RicardoCSR/MinervaProject/Render Nixie 1.png

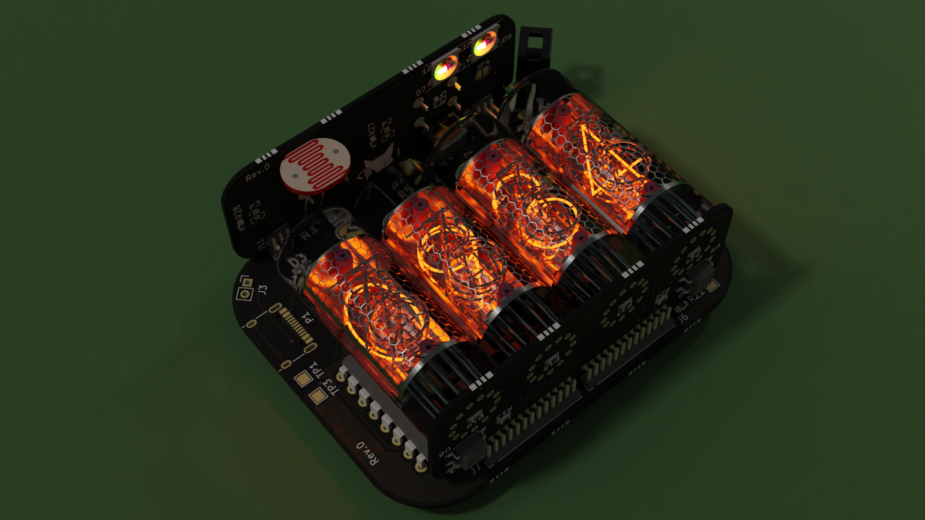
Render Nixie 1.png
