RicardoCSR/MinervaProject/Render 1.png

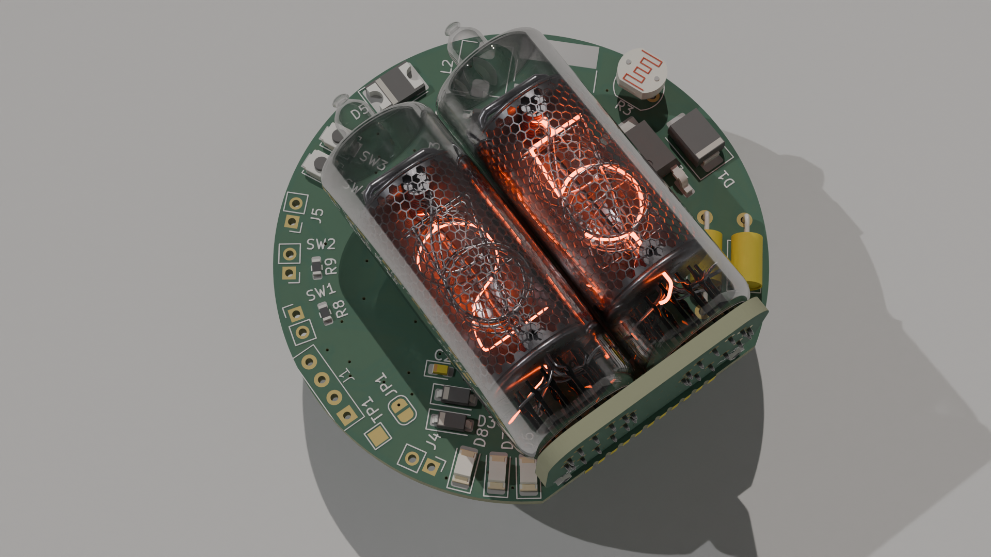
Render 1.png
