RicardoCSR/MinervaProject/Arquivos Web Minerva Clock/2.jpg

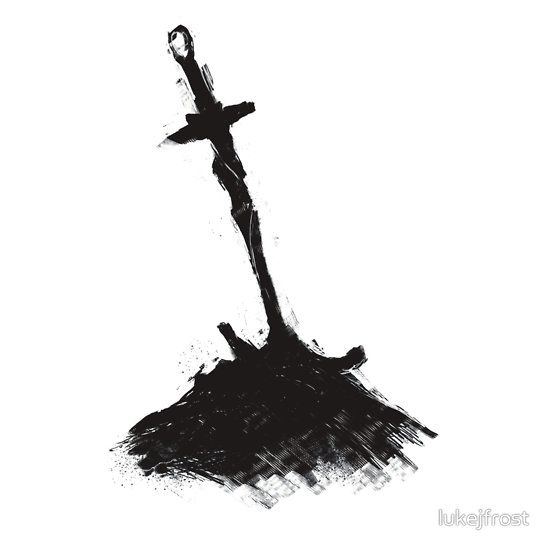
Arquivos Web Minerva Clock/2.jpg
