RicardoCSR/MinervaProject/Arquivos Web Minerva Clock/3.jpg

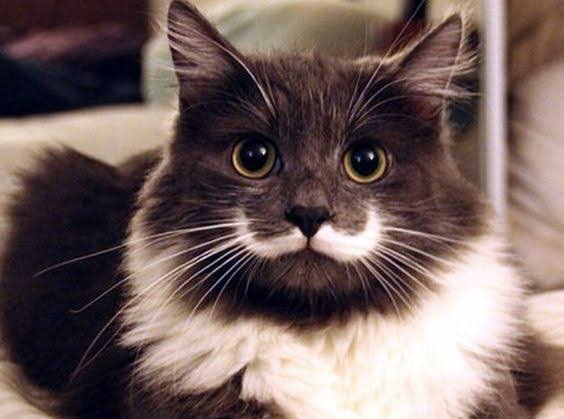
Arquivos Web Minerva Clock/3.jpg
