RicardoCSR/MinervaProject/Arquivos Web Minerva Clock/5.jpg

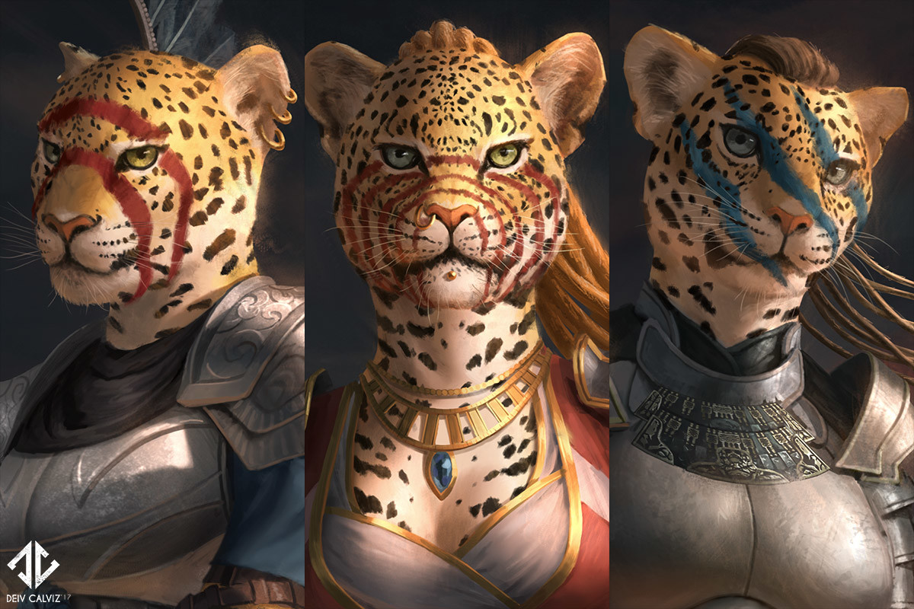
Arquivos Web Minerva Clock/5.jpg
