RicardoCSR/MinervaProject/Arquivos Web Minerva Clock/backgroundres.png

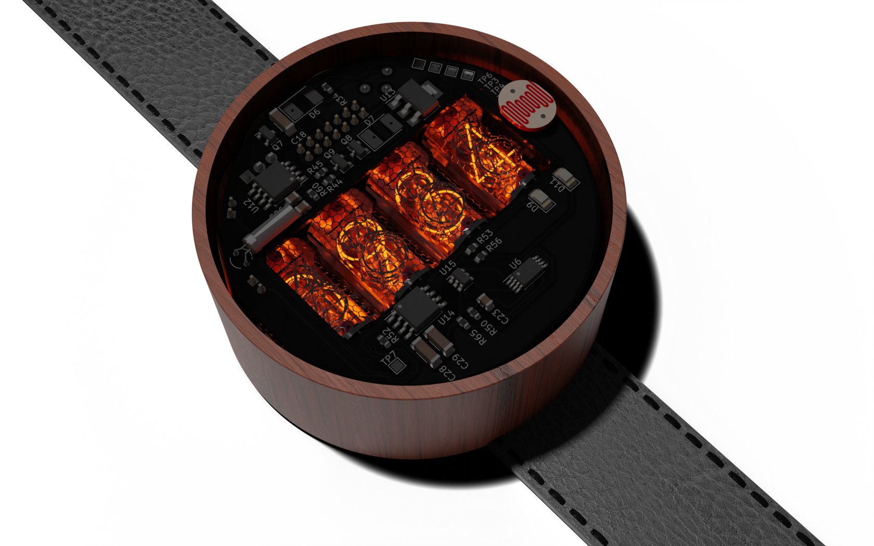
Arquivos Web Minerva Clock/backgroundres.png
