RicardoCSR/MinervaProject/ESP32 Conf 232.webp

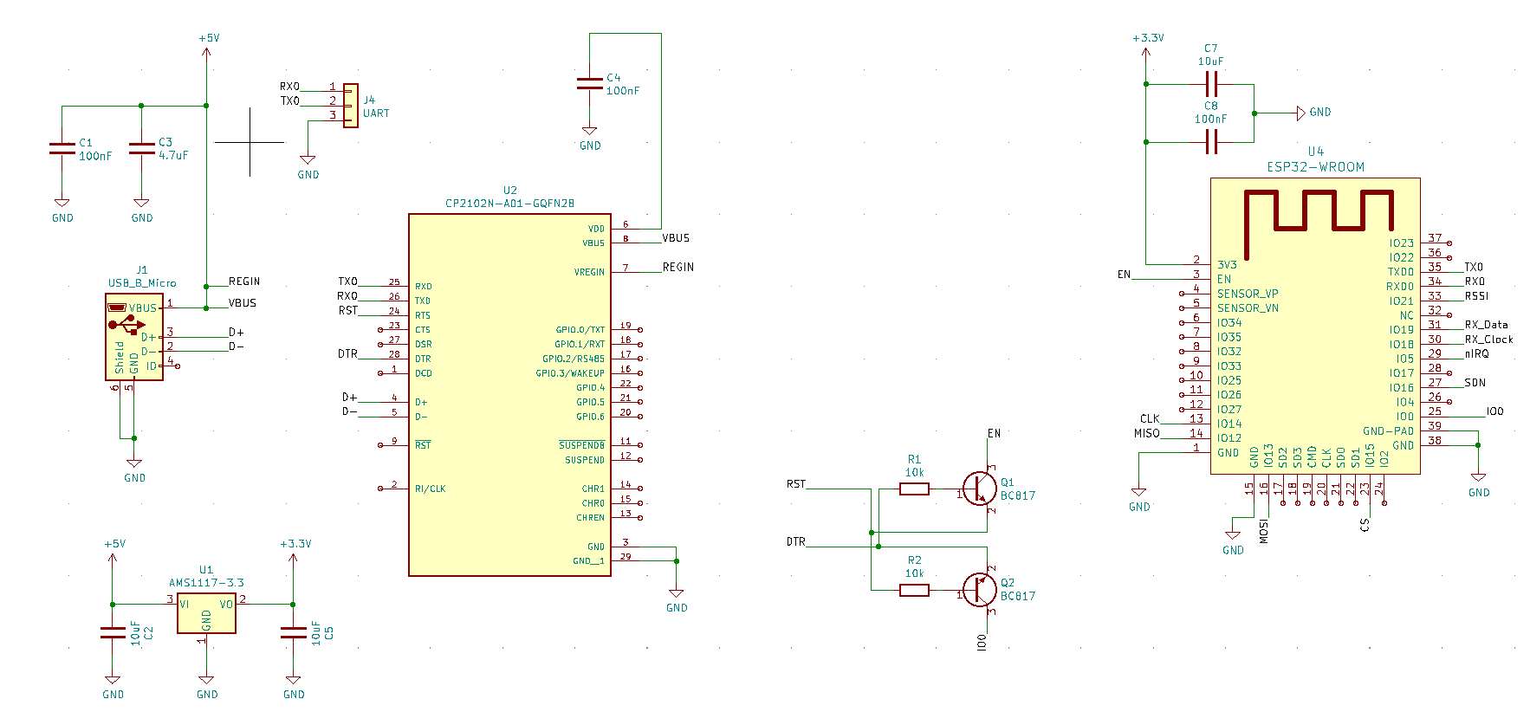
ESP32 Conf 232.webp
