RicardoCSR/MinervaProject/Imagens/Plano Fundo/Nixie.png

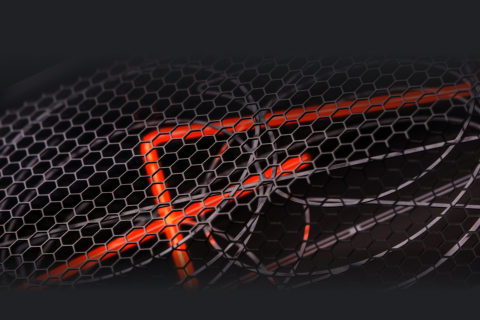
Imagens/Plano Fundo/Nixie.png
