RicardoCSR/MinervaProject/Web Server/Frame 61.jpg

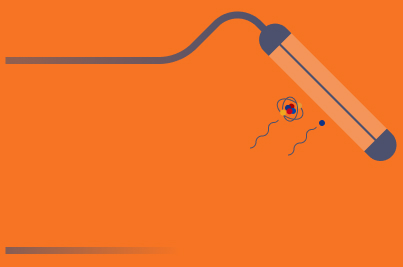
Web Server/Frame 61.jpg
