RicardoCSR/MinervaProject/Web Server/Frame 62.jpg

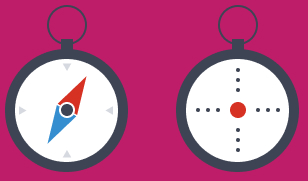
Web Server/Frame 62.jpg
