RicardoCSR/MinervaProject/Web Server/Frame 63.jpg

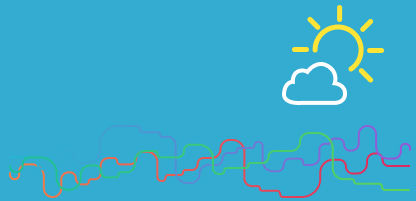
Web Server/Frame 63.jpg
