RicardoCSR/MinervaProject/Web Server/Frame 64.jpg

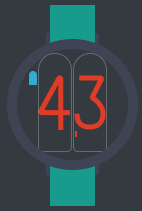
Web Server/Frame 64.jpg
