RicardoCSR/MinervaProject/Web Server/WebServer/blackmufox.jpg

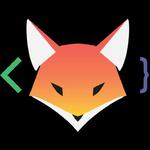
Web Server/WebServer/blackmufox.jpg
