RicardoCSR/MinervaProject/Web Server/WebServer/blackmufoxpng.png

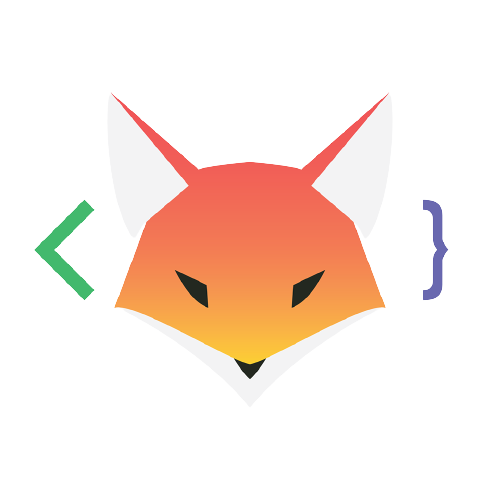
Web Server/WebServer/blackmufoxpng.png
