RicardoCSR/MinervaProject/Web Server/WebServer/simplemufox.jpg

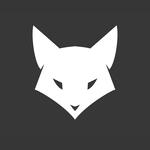
Web Server/WebServer/simplemufox.jpg
