RicardoCSR/MinervaProject/Relogio_STM32_TFT_Nixie.ino

 /*
Lista Terminais Utilizados STM32F401CCU6

BRANCO -    COMANDOS (BOTOES)
VERDE -     GNDS   
AMARELO -   3V3
VERMELHO -  5V
PRETO -     PWM
LARANJA -   SPI
ROXO -      GEIGER     
AZUL -      NIXIE

Caracteristica

SN74141 : True Table
calcDay1 C B A #
L,L,L,L 0
L,L,L,H 1
L,L,H,L 2
L,L,H,H 3
L,H,L,L 4
L,H,L,H 5
L,H,H,L 6
L,H,H,H 7
H,L,L,L 8
H,L,L,H 9
H,L,H,L N
H,L,H,H N
H,H,L,L N
H,H,L,H N
H,H,H,L N
H,H,H,H N

*/

// DADOS RELOGIO
int fulltime;                   // Armazena Horario 4 Digitos Processado
int hours = 0;                  // Armazena Horario Horas
int mins = 0;                   // Armazena Horario Minutos
byte compareTimeHour;           // Armazena Horario do Display
byte compareTimeMins;           // Armazena Horario do Display
byte compareTimeSecs;           // Armazena Horario do Display

byte compareSecs = 0;           // Armazena Horario Menu de Ajuste Relogio
byte compareMins = 0;           // Armazena Horario Menu de Ajuste Relogio
byte compareHour = 0;           // Armazena Horario Menu de Ajuste Relogio

byte compareDay = 0;            // Armazena Data Menu de Ajuste Calendario
byte compareMonth = 0;          // Armazena Data Menu de Ajuste Calendario
int compareYear = 0;            // Armazena Data Menu de Ajuste Calendario

byte hourBias;                  // Byte para Long horas x fuso (12 ~ 24)
byte minuteBias;                // Byte para Long minutos x 60 
byte secsBias;                  // Byte para Long segundos x 60
int secs;                       // Armazena Horario Segundos sem conversão

// NIVEL DE BATERIA E WIFI   
byte compareUpdateBattery;      // Armazena atualização de updateBattery
byte compareUpdateWiFi;         // Armazena atualização de updateBattery


// DADOS TOUCHSCREEN
int xMax;
int xMin;
int yMax;
int yMin;

// DADOS TIMERS
unsigned long period = 0;

// VALORES AJUSTAVEIS PELO USUÁRIO
byte logoTime = 3;

byte backgroundSetup = 0;
// backgroundSetup = 0 Programa Fundo Preto e Colorido.
// backgroundSetup = 1 Programa Fundo Branco e Colorido.
// backgroundSetup = 2 Programa Fundo Preto.
// backgroundSetup = 3 Programa Fundo Branco.

byte batteryStyleMode = 0;
// batteryStyleMode = 0 Estilo 1 de Bateria.
// batteryStyleMode = 1 Estilo 2 de Bateria.
// batteryStyleMode = 2 Estilo 3 de Bateria.
// batteryStyleMode = 3 Estilo 4 de Bateria.

byte lockStyle = 0;
// lockStyle = 0 Estilo 1 de Trava.
// lockStyle = 1 Estilo 2 de Trava.

int day;                        // Armazena dados de dia calendario
int month;                      // Armazena dados de mes calendario
int year;                       // Armazena dados de ano calendario
int startDay = 0;               // Identifica o 1 dia da semana
byte Week = 0;                  // Armazena Semana do ano
int dayWeek = 0;                // Armazena Dia do ano
int monthLengh = 0;             // Armazena o tamanho do Mes
int newDayStart = 0;            // Armazena o Dia do inicio da semana
int newWeekStart = 0;           // Armazena a posicao da Semana 
byte weekYear = 1;              // Armazena semana do mes calendario
int udpateCalendar;             // Armazena o dia para atualizacao do calendario

byte fuso = 1;                  
//fuso = 0 12 Horas  
//fuso = 1 24 Horas

// GERACAO DE GRAFICOS
int secsCalcGeiger = 0;         // Armazena segundos marcação gráfico Geiger
int minsCalcGeiger = 0;         // Armazena minutos marcação gráfico Geiger
int minsCalcTemp = 0;           // Armazena Horario marcação gráfico Temperatura
int minsCalcHumi = 0;           // Armazena Horario marcação gráfico Umidade
int minsCalcPres = 0;           // Armazena Horario marcação gráfico Pressão Atmosferica

int calcGeiger = 0;             // Armazena dado de Contagem para geigerCalc
int calcTemp = 0;               // Armazena dado de Contagem para tempCalc
int calcHumi = 0;               // Armazena dado de Contagem para humiCalc
int calcPres = 0;               // Armazena dado de Contagem para presCalc

int bankGeiger = 0;             // Armazena dado da posição do Gráfico em uso
int bankTemp = 0;               // Armazena dado da posição do Gráfico em uso
int bankHumi = 0;               // Armazena dado da posição do Gráfico em uso
int bankPres = 0;               // Armazena dado da posição do Gráfico em uso

byte functGeiger = 0;


int writerGeiger = 0;           // Armazena dado da posição do Gráfico em não uso
int writerTemp = 0;             // Armazena dado da posição do Gráfico em não uso
int writerHumi = 0;             // Armazena dado da posição do Gráfico em não uso
int writerPres = 0;             // Armazena dado da posição do Gráfico em não uso

int arrayGeiger [400] = {0};     // Armazena dados de Geiger
int arrayTemp [400] = {0};       // Armazena dados de Temperatura 
int arrayHumi [400] = {0};       // Armazena dados de Umidade 
int arrayPres [400] = {0};       // Armazena dados de Pressão Atmosferica

byte encoderPos = 0;
byte lastPos;
byte readClock;
boolean bCW;

int pressingDuration = 500;     // Tempo do botão Pressionado em Millis

unsigned long timerMode = 0;    // Armazena tempo atual
unsigned long touchMode = 0;    // Armazena tempo Touch

int minimumBrightness = 25;
int maximumBrightness = 255;

byte displayMode = 0;
// displayMode = 0 Sistema aguardando comando
// displayMode = 1 Habilita entrada do Menu
// displayMode = 2 Habilita saida do Menu

byte displayTFT = 0;     
// displayTFT = 0 Sistema aguardando comando

// BANCO DE DADOS DE COMPARADORES
byte logoStarted = 0;
// logoStarted = 0 Tela de Abertura ativado.
// logoStarted = 1 Tela de Abertura desativado.

byte powerCharger = 0;          
// powerCharger = 0 Carregador Desconectado
// powerCharger = 1 Carregador Conectado

byte screenLoad = 0;
// screenLoad = 0 Tela inicia o carregamento.
// screenLoad = 1 Tela para o carregamento.

byte updateBattery = 0;
// updateBattery = 0 Apresentação Bateria Level 1
// updateBattery = 1 Apresentação Bateria Level 2
// updateBattery = 2 Apresentação Bateria Level 3
// updateBattery = 3 Apresentação Bateria Level 4
// updateBattery = 4 Apresentação Bateria Level 5
// updateBattery = 5 Apresentação Bateria Level 6
// updateBattery = 6 Apresentação Bateria Level 7

byte wifiStyle = 0;
// wifiStyle = 0 Design WiFi default
// wifiStyle = 1 Design WiFi 1
// wifiStyle = 2 Design WiFi 2
// wifiStyle = 3 Design WiFi 3

byte wifiRead = 0;
// wifiRead = 0 WiFi em alta potência
// wifiRead = 1 WiFi em media potência
// wifiRead = 2 WiFi em baixa potência
// wifiRead = 3 WiFi sem Sinal

byte dosimeterSelection = 1;
// dosimeterSelection = 1 
// dosimeterSelection = 2
// dosimeterSelection = 3 
// dosimeterSelection = 4 
// dosimeterSelection = 5 

byte telaMenu = 0;
// telaMenu = 0 Menu Principal
// telaMenu = 1 Tela  
// telaMenu = 2 Tela  
// telaMenu = 3 Tela  
// telaMenu = 4 Tela  
// telaMenu = 5 Tela  
// telaMenu = 6 Tela  
// telaMenu = 7 Tela  
// telaMenu = 8 Tela  
// telaMenu = 9 Tela  
// telaMenu = 10 Tela 
// telaMenu = 11 Tela 
// telaMenu = 12 Tela 
// telaMenu = 13 Tela 
// telaMenu = 14 Tela 
// telaMenu = 15 Tela 

byte touchSet = 0; // Indica se o touch esta calibrado
// touchSet = 0 Display nao calibrado
// touchSet = 1 Display calibrado
// touchSet = 2 Usando os valores do DESENVOLVEDOR no setup()
// touchSet = 3 Em finalizacao de calibracao

bool squareEnd = 0;
bool roundEnd = 1;

// ------------------------------ CONFIGURACAO DOS PINOS DE SENSORES E DISPLAY --------

int pinBatteryRead;
int pinBatteryCharger;         // Pino de Leitura da Bateria

// ------------------------------ CORES DISPLAY RGB 555 -------------------------------

uint16_t blue_battery = 0x16BB;         //0x15D9E1
uint16_t green_battery = 0x1F22;        //0x19E710
uint16_t yellow_battery = 0xEF02;       //0xF4E317
uint16_t yellowed_battery = 0xF523;     //0xF7A619
uint16_t orange_battery = 0xEB84;       //0xF67423
uint16_t red_battery = 0xEA69;          //0xEF4D4F
uint16_t charge_battery = 0x1F01;       //0x1AE510

uint16_t januaryColor = 0x21D1;         //0x27398F
uint16_t februeryColor = 0x0B35;        //0x0B69B1       
uint16_t marchColor = 0x14D1;           //0x189B8D
uint16_t aprilColor = 0x5DD1;           //0x5FBC8C
uint16_t mayColor = 0xF5AA;             //0xF8B958
uint16_t juneColor = 0xF4A6;            //0xE49837
uint16_t julyColor = 0xD264;            //0xDE5028
uint16_t augustColor = 0xD8E4;          //0xE02028
uint16_t septemberColor = 0xE0CB;       //0xE91B5B
uint16_t octoberColor = 0xB8EC;         //0xBE1D69
uint16_t novemberColor = 0x3232;        //0x344698
uint16_t decemberColor = 0x296F;        //0x31307E

uint16_t nixieColor = 0xD264;           //0xDE4E28
uint16_t dosimeterColor = 0xF234;       //0xFE48AA
uint16_t highValueColor = 0xD94B;       //0xE1295F

uint16_t middleTimeGraph = 0x7BEF;      //0x7E7E7E

uint16_t wifi_level3 = 0x16BB;          //0x15D9E2
uint16_t wifi_level2 = 0x053D;          //0x04A7F2
uint16_t wifi_level1 = 0x0B35;          //0x0B69B1

uint16_t wifi_off3 = 0x9CF3;            //0x9F9F9F
uint16_t wifi_off2 = 0x7BEF;            //0x7E7E7E
uint16_t wifi_off1 = 0x52AA;            //0x555555

uint16_t geigerLevel1 = 0x362F;         //0x39C87E
uint16_t geigerLevel2 = 0xFF06;         //0xFFE437
uint16_t geigerLevel3 = 0xD8E4;         //0xE02028
uint16_t geigerLevel = 0xEB84;          //0xF67423

uint16_t geigerColor;
uint16_t geigerColor1 = 0xFDA0;         //0xFFB801
uint16_t geigerColor2 = 0xDCA6;         //0xE49837

uint16_t luxColor1 = 0xFF06;            //0xFFE437
uint16_t luxColor2 = 0xFDA0;            //0xFFB801

uint16_t temperatureColor;
uint16_t temperatureColor1 = 0xDCA6;    //0xE49837
uint16_t temperatureColor2 = 0xD12B;    //0xDE2662

uint16_t humidityColor;
uint16_t humidityColor1 = 0x25B9;       //0x25B7D0
uint16_t humidityColor2 = 0x929A;       //0x9A54D8

uint16_t menuSelection = 0x16BB;        //0x15D9E2
uint16_t profileColor = 0x5DD1;         //0x5FBC8C

uint16_t pressureColor;
uint16_t pressureColor1 = 0x76A7;       //0x77DA3F
uint16_t pressureColor2 = 0x1DF2;       //0x1BBF9A

uint16_t springMenu = 0x9669;           //0x9AD24D
uint16_t summerMenu = 0xFF06;           //0xFFE437
uint16_t autumnMenu = 0xFDA0;           //0xFFB801
uint16_t winterMenu = 0x8E3D;           //0x90CAEF
uint16_t seasonMenu;

uint16_t drizzleColor = 0xCF5E;         //0xD0EEFD
uint16_t rainColor = 0x8E3D;            //0x90CAEF
uint16_t sunColor = 0xFF06;             //0xFFE437

uint16_t blackScript = 0x2104;          //0x202124
uint16_t greyScript = 0x94B2;           //0x969696
uint16_t greywhite = 0xDF1B;            //0xE6E6E6
uint16_t whiteScript = 0xFFFF;          //0xFFFFFF
uint16_t redScript = 0xEA69;            //0xEF4D4F
uint16_t yellowScript = 0xFDA0;         //0xFFB801
uint16_t greenScript = 0x1F01;          //0x1AE510
uint16_t blueScript = 0x0B35;           //0x0B69B1

uint16_t icon_1 = 0xEB84;               //0xF67423
uint16_t icon_2 = 0xED23;               //0xF1A71F
uint16_t icon_3 = 0xE2E9;               //0xEB6052
uint16_t icon_4 = 0x5DD1;               //0x5FBC8D
uint16_t icon_5 = 0xE0CB;               //0xE91B5B
uint16_t icon_6 = 0xE2E9;               //0xEB6052
uint16_t icon_7 = 0x566B;               //0x58D160
uint16_t icon_8 = 0x3559;               //0x33ACD1
uint16_t icon_9 = 0xDCA6;               //0xE49837
uint16_t icon_10 = 0x16BB;              //0x15D9E2
uint16_t icon_11 = 0x14D1;              //0x189B8D
uint16_t icon_12 = 0xB8EC;              //0xBE1D69
uint16_t icon_13 = 0x31C7;              //0x343A40
uint16_t icon_14 = 0x929A;              //0x9A54D8
uint16_t icon_15 = 0x634C;              //0x6A6A6A

uint16_t icon_black = 0x8450;           //0x8A8A8A
uint16_t icon_white = 0xD6BA;           //0xD9D9D9

// Font file is stored in SPIFFS
#define FS_NO_GLOBALS
#include <FS.h>
#include <TFT_eSPI.h> 
#include <SPI.h>
#include "MapFloat.h"
#include <Wire.h>
#include "Adafruit_GFX.h"

#include <WiFi.h>

#include <stdint.h>

#include <EasyColor.h>

#include "Imagens.h"

#include "Lato_Bold_48.h"
#include "Lato_Regular_24.h"
#include "Lato_Regular_14.h"
#include "Lato_Regular_12.h"
#include "Lato_Regular_10.h"

#define latoBold48 &Lato_Bold_48
#define latoRegular24 &Lato_Regular_24
#define latoRegular14 &Lato_Regular_14
#define latoRegular12 &Lato_Regular_12
#define latoRegular10 &Lato_Regular_10

#define pinOnOff 16
#define pinSet 17
#define pinBL 25

#define GFXFF 1
  // TL_DATUM = Top left (default)
  // TC_DATUM = Top center
  // TR_DATUM = Top right
  // ML_DATUM = Middle left
  // MC_DATUM = Middle center
  // MR_DATUM = Middle right
  // BL_DATUM = Bottom left
  // BC_DATUM = Bottom center
  // BR_DATUM = Bottom right
  // L_BASELINE = Left character baseline (Line the 'A' character would sit on)
  // C_BASELINE = Centre character baseline
  // R_BASELINE = Right character baseline

// ------------------------------- INSTANCIAS DAS BIBLIOTECAS --------------------------
    
    TFT_eSPI tft = TFT_eSPI();      // Could invoke custom library declaring width and height
    TFT_eSPI_Button button;            // Could invoke button class and create all the button objects
    EasyColor rgb2rgb;                 //Conversão de e para RGB888/RGB565

void setup() {
  Serial.begin(115200);
  Serial.println("Sistema Inicializado");
  tft.init();
  tft.setRotation(1);

  pinMode(pinOnOff, INPUT_PULLUP);
  pinMode(pinSet, INPUT_PULLUP);

  if (!SPIFFS.begin()) {
    Serial.println("SPIFFS initialisation failed!");
    while (1) yield(); // Stay here twiddling thumbs waiting
  }
  listFiles(); // Lists the files so you can see what is in the SPIFFS

  if (touchSet == 2) {
    uint16_t calData[5] = { 223, 3675, 227, 3503, 7 };
    tft.setTouch(calData);
  }

  if (fuso == 1) {
    fuso = 23;
  } else {
    fuso = 11;
  }

  hours = 0;
  mins = 0;
  day = 1;
  month = 1;
  year = 2023;

  updateClock();
}



unsigned long UtlTime;
unsigned long timeSystem;
unsigned long timePressed;
unsigned long timePointLenghText;
unsigned long timeLoadScreen;


int dosimetervalue = 0;
byte geigerCurve = 0;
byte updateGeigerCurve = 0;
byte arrayDosi [480] = {0};  

byte i = 0;  // ATUALIZACAO VISUAL DATA E HORA 
byte language = 1; // TELA DE ABERTURA

uint16_t x = 0, y = 0; // To store the touch coordinates

// -------------------------- DATA BOTOES -----------------

  byte switchPressedRecalibrate = 0; 
  // switchPressedRecalibrate = 0 Aguardando comando
  // switchPressedRecalibrate = 1 Tela de Calibracao

  byte switchPressedTest = 0;
  // switchPressedTest = 0 Aguardando comando
  // switchPressedTest = 1 Tela de Teste do Touch

  byte switchPressedExit = 0;
  // switchPressedExit = 0 Aguardando comando
  // switchPressedExit = 1 Saida da calibracao para welcome()

  byte touchScreenMode = 0;
  // switchPressedExit = 0 Aguardando comando
  // switchPressedExit = 1 Habilita o testCalibration()

  byte switchLanguage = 0;
  // switchLanguage = 0 Aguardando comando
  // switchLanguage = 1 Altera valor de language

  byte switchStartWelcome = 0;
  // swtichStartWelcome = 0 Aguardando comando
  // swtichStartWelcome = 1 Saida de welcome para knowname()

  byte switchInputName = 0;
  // swtichStartWelcome = 0 Aguardando comando
  // swtichStartWelcome = 1 Habita o keyboard()

  byte switchMenuStart = 0;
  // swtichStartWelcome = 0 Aguardando comando
  // swtichStartWelcome = 1 Habita o welcome()
  // swtichStartWelcome = 2 Habita o knowname()
  // swtichStartWelcome = 3 Habita o profileimage()
  // swtichStartWelcome = 4 Habita o internetAcess()
  // swtichStartWelcome = 5 Habita o startProgram()

  byte switchKeyboard = 0;
  // switchKeyboard = 0 Aguardando comando
  // switchKeyboard = 1 Habita o knowname()

  byte keyboardClose = 0;
  // keyboardClose = 0 Aguardando comando
  // keyboardClose = 1 Habita o knowname()

  byte swithContinueKnowname = 0;
  // swithContinueKnowname = 0 Aguardando comando
  // swithContinueKnowname = 1 Habita o profileimage()

  byte switchCaps = 0;
  // switchCaps = 0 Aguardando comando
  // switchCaps = 1 Habita o CAPSLOCK

  byte languageScreen = 0;
  // languageScreen = 0 Aguardando comando
  // languageScreen = 1 Habilita alteracao da byte language

  byte switchSearchWiFi = 0;
  // switchSearchWiFi = 0 Aguardando Comando
  // switchSearchWiFi = 1 Habilita procura de rede Wi-Fi

  byte switchAcessWiFi = 0;
  // switchAcessWiFi = 0 Aguardando Comando
  // switchAcessWiFi = 1 Habilita conexao com a Rede Wi-Fi selecionada

  byte switchSelectWiFi = 0;
  // switchSelectWiFi = 0 Aguardando comando
  // switchSelectWiFi = 1 Habita o menuNetworks()

  byte switchMenuNetworks = 0;
  // switchMenuNetworks = 0 Aguardando comando
  // switchMenuNetworks = 1 Habilita menuNetworks()

  byte selectedNetwork = 0;
  // selectedNetwork = 0 Aguardando comando
  // selectedNetwork = 1 Marca a rede selecionada menunetworks()

  byte selectedSSID = 0;
  // selectedSSID = 0 Aguardando comando
  // selectedSSID = 1 Marca a posicao da rede selecionada

  byte switchPasswordWiFi = 0;
  // switchPasswordWiFi = 0 Aguardando comando
  // switchPasswordWiFi = 1 Habita o passwordWiFi()

#define nameLenght 15
#define passwordLenght 24
int lenghtText = 0;
char textKnowName [nameLenght] = {0};
char textKnowPassword [passwordLenght] = {0};
String userName;
String password;

char key;

int numNetworks;
int numberSSID;

byte selectNetwork = 0;
byte menuStartNetwork = 0;
byte menuEndNetwork = numNetworks - 1;



void loop(void) {
  // ------------------------------ botao --------------
    int powerDisplay = digitalRead(pinOnOff);
    if (powerDisplay == HIGH) {
      dacWrite(pinBL, 255);
    } else {
      dacWrite(pinBL, 100);
    }

  // ------------------------------ touchScreen OPERACIONAL ----------------------
    
    uint16_t t_x = 0, t_y = 0; 

    bool pressed = tft.getTouch(&t_x, &t_y);


















    if (pressed) {
      if (timeSystem - timePressed >= 250) {
        Serial.print("x, y, z = ");
        Serial.print(x);
        Serial.print(",");
        Serial.print(y);
        Serial.print(",");
        Serial.printf("%i \n", tft.getTouchRawZ()); 
        timePressed = timeSystem;
      
  // ------------------------------ TOUCHSCREEN DISPLAY TFT 16 E 17 ---------------------
        if (displayTFT == 16 || displayTFT == 17) {
          touchFillRoundRect(70, 250, 100, 30, 5, nixieColor, blackScript, switchPressedRecalibrate);
          tft.setTextDatum(MC_DATUM);
          tft.setTextColor(whiteScript, blackScript);
          smoothText("Lato_Regular_14");
          tft.drawString("Recalibrar", 120, 266, GFXFF);
          if (switchPressedRecalibrate == 1) {
            switchPressedRecalibrate = 0;
            touchScreenMode = 0;
            touch_calibrate();
          }

          touchFillRoundRect(190, 250, 100, 30, 5, autumnMenu, blackScript, switchPressedTest);
          Serial.print("switchPressedTest: ");
          Serial.println(switchPressedTest);
          if (touchScreenMode == 0) {
            tft.setTextColor(whiteScript, nixieColor);
            tft.drawString("Testar", 240, 266, GFXFF);
          }
          if (switchPressedTest == 1) {
            testCalibration();
          } 

          touchFillRoundRect(310, 250, 100, 30, 5, winterMenu, blackScript, switchPressedExit);
          if (switchPressedExit == 1) {
            switchPressedExit = 0;
            touchScreenMode = 0;
            displayTFT = 18;
            tft.fillScreen(blackScript);
            welcome();
          }
        }

  // ------------------------------ WELCOME DISPLAY TFT 18 ---------------------
        if ((displayTFT == 18) && (millis() - timeLoadScreen >= 1000)) {
          timeLoadScreen = millis();
          touchFillRect(390, 280, 90, 40, blackScript, blackScript, languageScreen);
          if (languageScreen == 1) {
            tft.fillScreen(blackScript);
            if (language == 1) {
              language = 0;
              languageScreen = 0;
              welcome();
            } else {
              language = 1;
              languageScreen = 0;
              welcome();
            }
          }
          
          touchFillRect(190, 232, 100, 30, blackScript, blackScript, switchStartWelcome);
          if (switchStartWelcome == 1) {
            switchStartWelcome = 0;
            displayTFT = 19;
            tft.fillScreen(blackScript);
            knowname();
          }
          updateClock();
          wifiLevel();
          batteryLevel();
          lockLevel();
        }

  // ------------------------------ KNOWNAME DISPLAY TFT 19 ---------------------
        if ((displayTFT == 19) && (millis() - timeLoadScreen >= 1000)) {
          timeLoadScreen = millis();
          touchFillRect(390, 280, 90, 40, blackScript, blackScript, languageScreen);
          if (languageScreen == 1) {
            tft.fillScreen(blackScript);
            if (language == 1) {
              language = 0;
              languageScreen = 0;
              knowname();
            } else {
              language = 1;
              languageScreen = 0;
              knowname();
            }
          }

          touchFillRoundRect(115, 150, 250, 30, 5, whiteScript, blackScript, switchInputName);
          if (switchInputName == 1) {
            tft.fillScreen(blackScript);
            switchInputName = 0;
            displayTFT = 20;
            keyboard();
          }

          
          touchFillRoundRect(190, 232, 100, 30, 5, whiteScript, blackScript, swithContinueKnowname);
          if (swithContinueKnowname == 1) {
            displayTFT = 21;
            tft.fillScreen(blackScript);
            swithContinueKnowname = 0;
            profileimage();
          }
          

          touchCircle(454, 88, 10, whiteScript, wifi_off2, switchMenuStart);
          if (switchMenuStart == 1) {
            displayTFT = 18;
            tft.fillScreen(blackScript);
            switchMenuStart = 0;
            welcome();
          }
          updateClock();
          wifiLevel();
          batteryLevel();
          lockLevel();
        }

  // ------------------------------ KEYBOARD DISPLAY TFT 20 ---------------------
        if ((displayTFT == 20)  && (millis() - timeLoadScreen >= 500)) {
          timeLoadScreen = millis();
          touchFillRect(2, 240, 35, 35, wifi_off2, blackScript, switchCaps);
          touchFillRect(442, 240, 35, 35, wifi_off2, blackScript, switchCaps);
          if (x > 2 && x < 2 + 35 && y > 240 && y < 240 + 35) {
            tft.fillRect(0, 160, 480, 160, blackScript);
            keyboard();
          } 
          if (x > 2 && x < 2 + 35 && y > 240 && y < 240 + 35) {
            tft.fillRect(0, 160, 480, 160, blackScript);
            keyboard();
          }

          touchCircle(20, 90, 20, blackScript, blackScript, keyboardClose);
          if (keyboardClose == 1) {
            displayTFT = 20;
            keyboardClose = 0;
            if (displayTFT == 19) {
              tft.fillScreen(blackScript);
              knowname();
            } else if (displayTFT == 22) {
              tft.fillScreen(blackScript);
              internetAcess();
            }
          }
          updateClock();
          wifiLevel();
          batteryLevel();
          lockLevel();
          /*
          if (timeSystem - timePointLenghText >= 500) {

          }
          */

    // COLUNA 1 TECLADO
          if (x > 2 && x < 2 + 35 && y > 160 && y < 160 + 35) {
            if (switchCaps == 0) {
              textBoxName(113);
              Serial.println("q");
            } else {
              textBoxName(81);
              Serial.println("Q");
            }
          }
          if (x > 42 && x < 42 + 35 && y > 160 && y < 160 + 35) {
            if (switchCaps == 0) {
              textBoxName(119);
              Serial.println("w");
            } else {
              textBoxName(87);
              Serial.println("W");
            }
          }
          if (x > 82 && x < 82 + 35 && y > 160 && y < 160 + 35) {
            if (switchCaps == 0) {
              textBoxName(101);
              Serial.println("e");
            } else {
              textBoxName(69);
              Serial.println("E");
            }
          }
          if (x > 122 && x < 122 + 35 && y > 160 && y < 160 + 35) {
            if (switchCaps == 0) {
              textBoxName(114);
              Serial.println("r");
            } else {
              textBoxName(82);
              Serial.println("R");
            }
          }
          if (x > 162 && x < 162 + 35 && y > 160 && y < 160 + 35) {
            if (switchCaps == 0) {
              textBoxName(116);
              Serial.println("t");
            } else {
              textBoxName(84);
              Serial.println("T");
            }
          }
          if (x > 202 && x < 202 + 35 && y > 160 && y < 160 + 35) {
            if (switchCaps == 0) {
              textBoxName(121);
              Serial.println("y");
            } else {
              textBoxName(89);
              Serial.println("Y");
            }
          }
          if (x > 242 && x < 242 + 35 && y > 160 && y < 160 + 35) {
            if (switchCaps == 0) {
              textBoxName(117);
              Serial.println("u");
            } else {
              textBoxName(85);
              Serial.println("U");
            }
          }
          if (x > 282 && x < 282 + 35 && y > 160 && y < 160 + 35) {
            if (switchCaps == 0) {
              textBoxName(105);
              Serial.println("i");
            } else {
              textBoxName(73);
              Serial.println("I");
            }
          }
          if (x > 322 && x < 322 + 35 && y > 160 && y < 160 + 35) {
            if (switchCaps == 0) {
              textBoxName(111);
              Serial.println("o");
            } else {
              textBoxName(79);
              Serial.println("O");
            }
          }
          if (x > 362 && x < 362 + 35 && y > 160 && y < 160 + 35) {
            if (switchCaps == 0) {
              textBoxName(112);
              Serial.println("p");
            } else {
              textBoxName(80);
              Serial.println("P");
            }
          }
          if (x > 402 && x < 402 + 75 && y > 160 && y < 160 + 35) {
            textBoxName(8);
            Serial.println("Backspace");
          }

    // COLUNA 2 TECLADO
          if (x > 24 && x < 24 + 35 && y > 200 && y < 200 + 35) {
            if (switchCaps == 0) {
              textBoxName(97);
              Serial.println("a");
            } else {
              textBoxName(65);
              Serial.println("A");
            }
          }
          if (x > 64 && x < 64 + 35 && y > 200 && y < 200 + 35) {
            if (switchCaps == 0) {
              textBoxName(115);
              Serial.println("s");
            } else {
              textBoxName(83);
              Serial.println("S");
            }
          }
          if (x > 104 && x < 104 + 35 && y > 200 && y < 200 + 35) {
            if (switchCaps == 0) {
              textBoxName(100);
              Serial.println("d");
            } else {
              textBoxName(68);
              Serial.println("D");
            }
          }
          if (x > 144 && x < 144 + 35 && y > 200 && y < 200 + 35) {
            if (switchCaps == 0) {
              textBoxName(102);
              Serial.println("f");
            } else {
              textBoxName(70);
              Serial.println("F");
            }
          }
          if (x > 184 && x < 184 + 35 && y > 200 && y < 200 + 35) {
            if (switchCaps == 0) {
              textBoxName(103);
              Serial.println("g");
            } else {
              textBoxName(71);
              Serial.println("G");
            }
          }
          if (x > 224 && x < 224 + 35 && y > 200 && y < 200 + 35) {
            if (switchCaps == 0) {
              textBoxName(104);
              Serial.println("h");
            } else {
              textBoxName(72);
              Serial.println("H");
            }
          }
          if (x > 264 && x < 264 + 35 && y > 200 && y < 200 + 35) {
            if (switchCaps == 0) {
              textBoxName(106);
              Serial.println("j");
            } else {
              textBoxName(74);
              Serial.println("J");
            }
          }
          if (x > 304 && x < 304 + 35 && y > 200 && y < 200 + 35) {
            if (switchCaps == 0) {
              textBoxName(107);
              Serial.println("k");
            } else {
              textBoxName(75);
              Serial.println("K");
            }
          }
          if (x > 344 && x < 344 + 35 && y > 200 && y < 200 + 35) {
            if (switchCaps == 0) {
              textBoxName(108);
              Serial.println("l");
            } else {
              textBoxName(76);
              Serial.println("L");
            }
          }
          if (x > 384 && x < 384 + 35 && y > 200 && y < 200 + 35) {
            textBoxName(39);
            Serial.println("'");
          }
          if (x > 424 && x < 424 + 53 && y > 200 && y < 200 + 35) {
            textBoxName(10);
            Serial.println("Enter");
          }

    // COLUNA 3 TECLADO
          if (x > 42 && x < 42 + 35 && y > 240 && y < 240 + 35) {
            if (switchCaps == 0) {
              textBoxName(122);
              Serial.println("z");
            } else {
              textBoxName(90);
              Serial.println("Z");
            }
          }
          if (x > 82 && x < 82 + 35 && y > 240 && y < 240 + 35) {
            if (switchCaps == 0) {
              textBoxName(120);
              Serial.println("x");
            } else {
              textBoxName(88);
              Serial.println("X");
            }
          }
          if (x > 122 && x < 122 + 35 && y > 240 && y < 240 + 35) {
            if (switchCaps == 0) {
              textBoxName(99);
              Serial.println("c");
            } else {
              textBoxName(67);
              Serial.println("C");
            }
          }
          if (x > 162 && x < 162 + 35 && y > 240 && y < 240 + 35) {
            if (switchCaps == 0) {
              textBoxName(118);
              Serial.println("v");
            } else {
              textBoxName(86);
              Serial.println("V");
            }
          }
          if (x > 202 && x < 202 + 35 && y > 240 && y < 240 + 35) {
            if (switchCaps == 0) {
              textBoxName(98);
              Serial.println("b");
            } else {
              textBoxName(66);
              Serial.println("B");
            }
          }
          if (x > 242 && x < 242 + 35 && y > 240 && y < 240 + 35) {
            if (switchCaps == 0) {
              textBoxName(110);
              Serial.println("n");
            } else {
              textBoxName(78);
              Serial.println("N");
            }
          }
          if (x > 282 && x < 282 + 35 && y > 240 && y < 240 + 35) {
            if (switchCaps == 0) {
              textBoxName(109);
              Serial.println("m");
            } else {
              textBoxName(77);
              Serial.println("M");
            }
          }
          if (x > 322 && x < 322 + 35 && y > 240 && y < 240 + 35) {
            textBoxName(44);
            Serial.println(",");
          }
          if (x > 362 && x < 362 + 35 && y > 240 && y < 240 + 35) {
            textBoxName(46);
            Serial.println(".");
          }
          if (x > 402 && x < 402 + 35 && y > 240 && y < 240 + 35) {
            textBoxName(63);
            Serial.println("?");
          }
          if (x > 442 && x < 442 + 35 && y > 240 && y < 240 + 35) {
            textBoxName(127);
            Serial.println("Del");
          }

    // COLUNA 4 TECLADO
          if (x > 122 && x < 122 + 235 && y > 280 && y < 280 + 35) {
            textBoxName(32);
            Serial.println("Space");
          }
        }

  // ------------------------------ PROFILEIMAGE DISPLAY TFT 21 ---------------------
        if (displayTFT == 21 && (millis() - timeLoadScreen >= 500)) {
          timeLoadScreen = millis();
          touchFillRect(390, 280, 90, 40, blackScript, blackScript, languageScreen);
          if (languageScreen == 1) {
            tft.fillScreen(blackScript);
            if (language == 1) {
              language = 0;
              languageScreen = 0;
              profileimage();
            } else {
              language = 1;
              languageScreen = 0;
              profileimage();
            }
          } 


          touchCircle(454, 88, 10, whiteScript, wifi_off2, switchMenuStart);
          if (switchMenuStart == 1) {
            displayTFT = 18;
            tft.fillScreen(blackScript);
            switchMenuStart = 0;
            welcome();
          }

          touchCircle(454, 123, 10, whiteScript, wifi_off2, switchMenuStart);
          if (switchMenuStart == 1) {
            displayTFT = 19;
            tft.fillScreen(blackScript);
            switchMenuStart = 0;
            knowname();
          }

          touchFillRoundRect(190, 232, 100, 30, 5, whiteScript, blackScript, swithContinueKnowname);
          if (swithContinueKnowname == 1) {
            displayTFT = 22;
            tft.fillScreen(blackScript);
            swithContinueKnowname = 0;
            internetAcess();
          }
          updateClock();
          wifiLevel();
          batteryLevel();
          lockLevel();
        }

  // ------------------------------ INTERNETACESS DISPLAY TFT 22 ---------------------
        if (displayTFT == 22 && (millis() - timeLoadScreen >= 500)) {
          timeLoadScreen = millis();
          touchFillRect(390, 280, 90, 40, blackScript, blackScript, languageScreen);
          if (languageScreen == 1) {
            tft.fillScreen(blackScript);
            if (language == 1) {
              language = 0;
              languageScreen = 0;
              internetAcess();
            } else {
              language = 1;
              languageScreen = 0;
              internetAcess();
            }
          } 

          touchCircle(454, 88, 10, whiteScript, wifi_off2, switchMenuStart);
          if (switchMenuStart == 1) {
            displayTFT = 18;
            tft.fillScreen(blackScript);
            switchMenuStart = 0;
            welcome();
          }

          touchCircle(454, 123, 10, whiteScript, wifi_off2, switchMenuStart);
          if (switchMenuStart == 1) {
            displayTFT = 19;
            tft.fillScreen(blackScript);
            switchMenuStart = 0;
            knowname();
          }

          touchCircle(454, 158, 10, whiteScript, wifi_off2, switchMenuStart);
          if (switchMenuStart == 1) {
            displayTFT = 21;
            tft.fillScreen(blackScript);
            switchMenuStart = 0;
            profileimage();
          }

          if (numberSSID >= 0) {
            tft.setTextDatum(ML_DATUM);
            smoothText("Lato_Regular_14");
            tft.setTextColor(whiteScript, blackScript);
            tft.drawString(WiFi.SSID(numberSSID), 120, 127, GFXFF);
            tft.drawRoundRect(115, 161, 215, 30, 5, whiteScript);
          }

          if (x > 123 && x < 123 + 100 && y > 216 && y < 216 + 30) {
            switchSearchWiFi = 1;
            tft.setTextDatum(MC_DATUM);
            smoothText("Lato_Regular_14");
            if (language == 1) {
              tft.setTextColor(greyScript, humidityColor1);
              tft.drawString("SEARCH", 173, 232, GFXFF);
            } else {
              tft.setTextColor(greyScript, humidityColor1);
              tft.drawString("BUSCAR", 173, 232, GFXFF);
            }

            Serial.println("Procurando por redes Wi-Fi...");
            WiFi.mode(WIFI_STA);
            WiFi.disconnect();

            Serial.println("Redes encontradas:");
            numNetworks = WiFi.scanNetworks();
            switchSearchWiFi = 0;
            for (int i = 0; i < numNetworks; i++) { 
              Serial.print(i+1);
              Serial.print(": ");
              Serial.print(WiFi.SSID(i));
              Serial.print(" (");
              Serial.print(WiFi.RSSI(i));
              Serial.println(")");
            }

            if (numNetworks > 0) {
              tft.drawRoundRect(115, 112, 250, 30, 5, whiteScript);
              tft.fillTriangle(346, 123, 356, 123, 351, 132, whiteScript);
            } else {
              tft.drawRoundRect(115, 112, 250, 30, 5, greyScript);
              tft.fillTriangle(346, 123, 356, 123, 351, 132, greyScript);
            }

            if (language == 1) {
              tft.setTextColor(whiteScript, humidityColor1);
              tft.drawString("SEARCH", 173, 232, GFXFF);
            } else {
              tft.setTextColor(whiteScript, humidityColor1);
              tft.drawString("BUSCAR", 173, 232, GFXFF);
            }
          }

          touchRoundRect(115, 112, 250, 30, 5, greyScript, greyScript, switchSelectWiFi);
          if (switchSelectWiFi == 1 && numNetworks > 0) {
            displayTFT = 23;
            tft.fillScreen(blackScript);
            switchSelectWiFi = 0;
            menuNetworks();
          }

          touchRoundRect(115, 161, 215, 30, 5, whiteScript, blackScript, switchPasswordWiFi);
          if (switchPasswordWiFi == 1) {
            displayTFT = 24;
            tft.fillScreen(blackScript);
            switchPasswordWiFi = 0;
            keyboard();
          }

          updateClock();
          wifiLevel();
          batteryLevel();
          lockLevel();
        }

  // ------------------------------ MENUNETWORKS DISPLAY TFT 23 ---------------------
        if (displayTFT == 23 && (millis() - timeLoadScreen >= 500)) {
          timeLoadScreen = millis();
          touchFillRect(390, 280, 90, 40, blackScript, blackScript, languageScreen);
          if (languageScreen == 1) {
            tft.fillScreen(blackScript);
            if (language == 1) {
              language = 0;
              languageScreen = 0;
              menuNetworks();
            } else {
              language = 1;
              languageScreen = 0;
              menuNetworks();
            }
          } 

          touchCircle(454, 88, 10, whiteScript, wifi_off2, switchMenuStart);
          if (switchMenuStart == 1) {
            displayTFT = 18;
            tft.fillScreen(blackScript);
            switchMenuStart = 0;
            welcome();
          }

          touchCircle(454, 123, 10, whiteScript, wifi_off2, switchMenuStart);
          if (switchMenuStart == 1) {
            displayTFT = 19;
            tft.fillScreen(blackScript);
            switchMenuStart = 0;
            knowname();
          }

          touchCircle(454, 158, 10, whiteScript, wifi_off2, switchMenuStart);
          if (switchMenuStart == 1) {
            displayTFT = 21;
            tft.fillScreen(blackScript);
            switchMenuStart = 0;
            profileimage();
          }
          
          touchFillRect(129, 267, 100, 30, whiteScript, blackScript, switchMenuNetworks);
          if (switchMenuNetworks == 1) {
            displayTFT = 22;
            tft.fillScreen(blackScript);
            switchMenuNetworks = 0;
            internetAcess();
          }

          smoothText("Lato_Regular_14");
          tft.setTextDatum(MC_DATUM);
          if (language == 1 && selectedSSID > 0) {
            tft.setTextColor(whiteScript, pressureColor1);
            tft.drawString("CONFIRM", 299, 283, GFXFF);
          } else if (language == 0 && selectedSSID > 0) {
            tft.setTextColor(whiteScript, pressureColor1);
            tft.drawString("CONFIRMAR", 299, 283, GFXFF);
          }

          touchFillRect(249, 267, 100, 30, whiteScript, blackScript, selectedNetwork);
          if (selectedNetwork == 1 && selectedSSID > 0) {
            displayTFT = 22;
            tft.fillScreen(blackScript);
            selectedNetwork = 0;

            numberSSID = selectedSSID -1;

            selectedSSID = 0;
            internetAcess();
          }

          //touchFillRect(96, 94, 270, 30, 9, )
          if ((x > 96 && x < 96 + 270 && y > 94 && y < 94 + 30) && numNetworks >= 1) {
            selectedSSID = 1;
            tft.drawRoundRect(96, 94, 280, 30, 9, whiteScript);
            tft.drawRoundRect(96, 124, 280, 30, 9, blackScript);
            tft.drawRoundRect(96, 154, 280, 30, 9, blackScript);
            tft.drawRoundRect(96, 184, 280, 30, 9, blackScript);
            tft.drawRoundRect(96, 214, 280, 30, 9, blackScript);
          }
          if ((x > 96 && x < 96 + 270 && y > 124 && y < 124 + 30) && numNetworks >= 2) {
            selectedSSID = 2;
            tft.drawRoundRect(96, 94, 280, 30, 9, blackScript);
            tft.drawRoundRect(96, 124, 280, 30, 9, whiteScript);
            tft.drawRoundRect(96, 154, 280, 30, 9, blackScript);
            tft.drawRoundRect(96, 184, 280, 30, 9, blackScript);
            tft.drawRoundRect(96, 214, 280, 30, 9, blackScript);
          }
          if ((x > 96 && x < 96 + 270 && y > 154 && y < 154 + 30) && numNetworks >= 3) {
            selectedSSID = 3;
            tft.drawRoundRect(96, 94, 280, 30, 9, blackScript);
            tft.drawRoundRect(96, 124, 280, 30, 9, blackScript);
            tft.drawRoundRect(96, 154, 280, 30, 9, whiteScript);
            tft.drawRoundRect(96, 184, 280, 30, 9, blackScript);
            tft.drawRoundRect(96, 214, 280, 30, 9, blackScript);
          }
          if ((x > 96 && x < 96 + 270 && y > 184 && y < 184 + 30) && numNetworks >= 4) {
            selectedSSID = 4;
            tft.drawRoundRect(96, 94, 280, 30, 9, blackScript);
            tft.drawRoundRect(96, 124, 280, 30, 9, blackScript);
            tft.drawRoundRect(96, 154, 280, 30, 9, blackScript);
            tft.drawRoundRect(96, 184, 280, 30, 9, whiteScript);
            tft.drawRoundRect(96, 214, 280, 30, 9, blackScript);
          }
          if ((x > 96 && x < 96 + 270 && y > 214 && y < 214 + 30) && numNetworks >= 5) {
            selectedSSID = 5;
            tft.drawRoundRect(96, 94, 280, 30, 9, blackScript);
            tft.drawRoundRect(96, 124, 280, 30, 9, blackScript);
            tft.drawRoundRect(96, 154, 280, 30, 9, blackScript);
            tft.drawRoundRect(96, 184, 280, 30, 9, blackScript);
            tft.drawRoundRect(96, 214, 280, 30, 9, whiteScript);
          }


        
          updateClock();
          wifiLevel();
          batteryLevel();
          lockLevel();
        }



  // ------------------------------ KEYBOARD DISPLAY TFT 24 ------------
        /*if ((displayTFT == 24) && (millis() - timeLoadScreen >= 500)) {
          timeLoadScreen = millis();
          touchFillRect(2, 240, 35, 35, wifi_off2, blackScript, switchCaps);
          touchFillRect(442, 240, 35, 35, wifi_off2, blackScript, switchCaps);
          if (x > 2 && x < 2 + 35 && y > 240 && y < 240 + 35) {
            tft.fillRect(0, 160, 480, 160, blackScript);
            keyboard();
          } 
          if (x > 2 && x < 2 + 35 && y > 240 && y < 240 + 35) {
            tft.fillRect(0, 160, 480, 160, blackScript);
            keyboard();
          }

          touchCircle(20, 90, 20, blackScript, blackScript, keyboardClose);
          if (keyboardClose == 1) {
            displayTFT = 22;
            keyboardClose = 0;
            tft.fillScreen(blackScript);
            internetAcess();
          }
          updateClock();
          wifiLevel();
          batteryLevel();
          lockLevel();
          
        }
        */

      }
    }

  // ------------------------ HORARIO VIA MILLIS() OPERACIONAL -----------------------
    timeSystem = millis();

    if(timeSystem - UtlTime >= 1000) {
      UtlTime = timeSystem;
      secs ++;
    }
    if(secs > 59) {
      secs = 0;
      mins = mins + 1;
      if(mins > 59) {
        hours = hours + 1;
        mins = 0;
        if(hours > 23) {
          day = day + 1;
          hours = 0;
          if( month ==1 || month == 3 || month == 5 || month == 7 || month == 8 || month == 10 || month == 12) {
            if(day > 31) {
              day = 1;
              month = month + 1;
              if(month > 12) {
                year = year + 1;
                month = 1;
              }
            }
          }
          else if(month == 2) {
            if(year%400 == 0) {
              if(day > 29) {
                day = 1;
                month = month + 1;
              }
            }
            else if((year%4==0) && (year%100!=0)) {
              if(day > 29) {
                day = 1;
                month = month + 1;
              }
            } else {
              if(day > 28) {
                day = 1;
                month = month + 1;
              }
            }
          } else {
            if(day > 30) {
              day = 1;
              month = month + 1;
            }
          }
        }
      }
    }

  // ------------------------ COMANDO DE LOGO ----------

    if (logoStarted == 0) {
      logoStarted = 1;
      startLogo();
      if (UtlTime - period >= logoTime * 1000) {
        period = UtlTime;
        if ((backgroundSetup == 1) || (backgroundSetup == 3)) {
          tft.fillRect(0, 0, 480, 320, whiteScript);
        } else {
          tft.fillRect(0, 0, 480, 320, blackScript);
        }
      }
    } 

  // ------------------------ PERFIL SETUP -----------
    switch (backgroundSetup) {
      case 1:
        // do something
      break;
      case 2:
        // do something
      break;
      case 3:
        // do something
      break; 
      default: 
        if (touchSet == 1) {
          defaultSetup();
        } else if (touchSet == 0){
          touch_calibrate();
        }
    } 

  // ------------------------ ATUALIZA RELOGIO SERIAL OPERACIONAL -----------
    if (secs != compareSecs) {
      compareSecs = secs;
      Serial.print(day);
      Serial.print("/");
      Serial.print(month);
      Serial.print("/");
      Serial.print(year); 
      Serial.print("     ");
      Serial.print(hours);
      Serial.print(":");
      Serial.print(mins);
      Serial.print(":");
      Serial.println(secs);  
    }

  // ------------------------ ATUALIZA GRAFICO DOSIMETRO GEIGER -------------------
    if (telaMenu == 3) {
      //33 - 433 X
      //78 - 196 Y
      if (dosimeterSelection == 1) {
        if (secsCalcGeiger != secs) {
          secsCalcGeiger = secs;
          switch(secs) {
            case 0: bankGeiger = 32; break;
            case 1: bankGeiger = 39; break;
            case 2: bankGeiger = 45; break;
            case 3: bankGeiger = 52; break;
            case 4: bankGeiger = 59; break;
            case 5: bankGeiger = 65; break;
            case 6: bankGeiger = 72; break;
            case 7: bankGeiger = 77; break;
            case 8: bankGeiger = 85; break;
            case 9: bankGeiger = 92; break;
            case 10: bankGeiger = 99; break;
            case 11: bankGeiger = 105; break;
            case 12: bankGeiger = 112; break;
            case 13: bankGeiger = 119; break;
            case 14: bankGeiger = 125; break;
            case 15: bankGeiger = 132; break;
            case 16: bankGeiger = 139; break;
            case 17: bankGeiger = 145; break;
            case 18: bankGeiger = 152; break;
            case 19: bankGeiger = 159; break;
            case 20: bankGeiger = 165; break;
            case 21: bankGeiger = 172; break;
            case 22: bankGeiger = 179; break;
            case 23: bankGeiger = 185; break;
            case 24: bankGeiger = 192; break;
            case 25: bankGeiger = 199; break;
            case 26: bankGeiger = 205; break;
            case 27: bankGeiger = 212; break;
            case 28: bankGeiger = 219; break;
            case 29: bankGeiger = 225; break;
            case 30: bankGeiger = 232; break;
            case 31: bankGeiger = 239; break;
            case 32: bankGeiger = 245; break;
            case 33: bankGeiger = 252; break;
            case 34: bankGeiger = 259; break;
            case 35: bankGeiger = 265; break;
            case 36: bankGeiger = 272; break;
            case 37: bankGeiger = 279; break;
            case 38: bankGeiger = 285; break;
            case 39: bankGeiger = 292; break;
            case 40: bankGeiger = 299; break;
            case 41: bankGeiger = 305; break;
            case 42: bankGeiger = 312; break;
            case 43: bankGeiger = 319; break;
            case 44: bankGeiger = 325; break;
            case 45: bankGeiger = 332; break;
            case 46: bankGeiger = 339; break;
            case 47: bankGeiger = 345; break;
            case 48: bankGeiger = 352; break;
            case 49: bankGeiger = 359; break;
            case 50: bankGeiger = 365; break;
            case 51: bankGeiger = 372; break;
            case 52: bankGeiger = 379; break;
            case 53: bankGeiger = 385; break;
            case 54: bankGeiger = 392; break;
            case 55: bankGeiger = 399; break;
            case 56: bankGeiger = 405; break;
            case 57: bankGeiger = 412; break;
            case 58: bankGeiger = 418; break;
            case 59: bankGeiger = 425; break;
          }
        }
      }
      if (dosimeterSelection == 2) {
        if (minsCalcGeiger != mins) {
          minsCalcGeiger = mins;
          switch(hours) {
            case 0: bankGeiger = 32; break; 
            case 1: bankGeiger = 48; break; 
            case 2: bankGeiger = 64; break; 
            case 3: bankGeiger = 82; break;
            case 4: bankGeiger = 98; break;
            case 5: bankGeiger = 114; break;
            case 6: bankGeiger = 132; break;
            case 7: bankGeiger = 148; break;
            case 8: bankGeiger = 164; break;
            case 9: bankGeiger = 182; break;
            case 10: bankGeiger = 198; break;
            case 11: bankGeiger = 214; break;
            case 12: bankGeiger = 232; break;
            case 13: bankGeiger = 248; break;
            case 14: bankGeiger = 264; break;
            case 15: bankGeiger = 282; break;
            case 16: bankGeiger = 298; break;
            case 17: bankGeiger = 314; break;
            case 18: bankGeiger = 332; break;
            case 19: bankGeiger = 348; break;
            case 20: bankGeiger = 364; break;
            case 21: bankGeiger = 382; break;
            case 22: bankGeiger = 398; break;
            case 23: bankGeiger = 414; break;
          }
          switch(mins) {
            case 3: bankGeiger = bankGeiger + 0; break;
            case 6: bankGeiger = bankGeiger + 1; break;
            case 10: bankGeiger = bankGeiger + 2; break;
            case 13: bankGeiger = bankGeiger + 3; break;
            case 16: bankGeiger = bankGeiger + 4; break;
            case 19: bankGeiger = bankGeiger + 5; break;
            case 22: bankGeiger = bankGeiger + 6; break;
            case 25: bankGeiger = bankGeiger + 7; break;
            case 28: bankGeiger = bankGeiger + 8; break;
            case 31: bankGeiger = bankGeiger + 9; break;
            case 36: bankGeiger = bankGeiger + 10; break;
            case 37: bankGeiger = bankGeiger + 11; break;
            case 40: bankGeiger = bankGeiger + 12; break;
            case 43: bankGeiger = bankGeiger + 13; break;
            case 46: bankGeiger = bankGeiger + 14; break;
            case 49: bankGeiger = bankGeiger + 15; break;
            case 53: bankGeiger = bankGeiger + 16; break;
            case 56: bankGeiger = bankGeiger + 17; break;
          }
        }
      }
      byte undoWriterGeiger;
      if (bankGeiger != writerGeiger) {
        functGeiger = map(random(0, 200), 0, 200, 196, 78); 
        undoWriterGeiger = writerGeiger - 1;
        writerGeiger = bankGeiger;
      }
      rgbColorGeiger();
      arrayDosi[writerGeiger] = functGeiger;
      //tft.drawPixel(bankGeiger, arrayDosi[writerGeiger], geigerColor);
      tft.drawLine(bankGeiger, arrayDosi[writerGeiger], bankGeiger - 6, arrayDosi[undoWriterGeiger], geigerColor);
    }

  // ------------------------ ATUALIZACAO CALENDARIO OPERACIONAL -----------
    if (day != udpateCalendar) {
      udpateCalendar = day;
      if (telaMenu == 4) {
        tft.fillRect(0, 65, 480, 255, blackScript);
        calendar();
      }
    }

}

void updateClock() {
  String stringHour = String(hours);
  String stringMin = String(mins);
  String stringDay = String(day);
  String stringMonth = String(month);
  String stringYear = String(year);

  String stringHourMin = String(hours - 1);
  String stringMinMin = String(mins - 1);
  String stringDayMin = String(day - 1);
  String stringMonthMin = String(month - 1);
  String stringYearMin = String(year - 1);
  
  if (displayTFT < 16) {
    if (hours != compareHour) {
      compareHour = hours;
      tft.setTextDatum(ML_DATUM);
      tft.setTextColor(blackScript, blackScript);
      smoothText("Lato_Regular_24");
      if ((hours > 1) && (hours < 10)) {
        tft.drawString("0", 219, 30, GFXFF);
        tft.drawString(stringHourMin, 234, 30, GFXFF);
      } else {
        tft.fillRect(219, 22, 28, 20, blackScript);
      }
      tft.setTextColor(whiteScript, blackScript);  
      if (hours < 10) {
        tft.drawString("0", 219, 30, GFXFF);
        tft.drawString(stringHour, 234, 30, GFXFF);
      } else {
        tft.drawString(stringHour, 219, 30, GFXFF);
      }
    }
    if (mins != compareMins) {
      compareMins = mins;
      tft.setTextDatum(ML_DATUM);
      tft.setTextColor(blackScript, blackScript);
      smoothText("Lato_Regular_24");
      if ((mins > 1) && (mins < 10)) {
        tft.drawString("0", 252, 30, GFXFF);
        tft.drawString(stringMinMin, 267, 30, GFXFF);
      } else {
        tft.fillRect(252, 22, 28, 20, blackScript);
      }
      tft.setTextColor(whiteScript, blackScript);  
      if (mins < 10) {
        tft.drawString("0", 252, 30, GFXFF);
        tft.drawString(":", 246, 30, GFXFF);
        tft.drawString(stringMin, 267, 30, GFXFF);
      } else {
        tft.drawString(":", 246, 30, GFXFF);
        tft.drawString(stringMin, 252, 30, GFXFF);
      }
    }

    if (day != compareDay) {
      compareDay = day;
      tft.setTextDatum(ML_DATUM);
      tft.setTextColor(blackScript, blackScript);
      smoothText("Lato_Regular_24");
      if ((day > 1) && (day < 10)) {
        tft.drawString("0", 77, 30, GFXFF);
        tft.drawString(stringDayMin, 92, 30, GFXFF);
      } else {
        tft.fillRect(77, 22, 28, 20, blackScript);
      }

      tft.setTextColor(whiteScript, blackScript);  
      if (day < 10) {
        tft.drawString("0", 77, 30, GFXFF);
        tft.drawString(stringDay, 92, 30, GFXFF);
      } else {
        tft.drawString(stringDay, 77, 30, GFXFF);
      }
    }

    if (month != compareMonth) {
      compareMonth = month;
      tft.setTextDatum(ML_DATUM);
      tft.setTextColor(blackScript, blackScript);
      smoothText("Lato_Regular_24");
      if ((month > 1) && (month < 10)) {
        tft.drawString("0", 110, 30, GFXFF);
        tft.drawString(stringMonthMin, 125, 30, GFXFF);
      } else {
        tft.fillRect(110, 22, 28, 20, blackScript);
      }

      tft.setTextColor(whiteScript, blackScript);  
  
      if (month < 10) {
        tft.drawString("0", 110, 30, GFXFF);
        tft.drawString(stringMonth, 125, 30, GFXFF);
      } else {
        tft.drawString(stringMonth, 110, 30, GFXFF);
      }
    }

    if (year != compareYear) {
      compareYear = year;
      tft.setTextDatum(ML_DATUM);
      tft.setTextColor(blackScript, blackScript);
      smoothText("Lato_Regular_24");
      tft.drawString(stringYearMin, 143, 30, GFXFF);

      tft.setTextColor(whiteScript, blackScript);  

      tft.drawString(stringYear, 143, 30, GFXFF);
    }
  } else if (displayTFT >= 18) {
    tft.setTextDatum(ML_DATUM);
    tft.setTextColor(blackScript, blackScript);
    smoothText("Lato_Regular_24");
    tft.setTextColor(whiteScript, blackScript);  
    if (hours < 10) {
      tft.drawString("0", 219, 30, GFXFF);
      tft.drawString(stringHour, 234, 30, GFXFF);
    } else {
      tft.drawString(stringHour, 219, 30, GFXFF);
    }

    if (mins < 10) {
      tft.drawString("0", 252, 30, GFXFF);
      tft.drawString(":", 246, 30, GFXFF);
      tft.drawString(stringMin, 267, 30, GFXFF);
    } else {
      tft.drawString(":", 246, 30, GFXFF);
      tft.drawString(stringMin, 252, 30, GFXFF);
    }

    if (day < 10) {
      tft.drawString("0", 77, 30, GFXFF);
      tft.drawString(stringDay, 92, 30, GFXFF);
    } else {
      tft.drawString(stringDay, 77, 30, GFXFF);
    }

    if (month < 10) {
      tft.drawString("0", 110, 30, GFXFF);
      tft.drawString(stringMonth, 125, 30, GFXFF);
    } else {
      tft.drawString(stringMonth, 110, 30, GFXFF);
    }

    tft.drawString(stringYear, 143, 30, GFXFF);
  }
}

void menuNetworks() {
  byte spaceText = 30;
  tft.fillCircle(454, 88, 10, greyScript);
  tft.fillCircle(454, 123, 10, greyScript);
  tft.fillCircle(454, 158, 10, greyScript);
  tft.fillCircle(454, 193, 10, whiteScript);
  tft.fillCircle(454, 228, 10, greyScript);

  tft.drawRoundRect(95, 93, 300, 152, 10, whiteScript);

  if (numNetworks > 5) {
    tft.fillTriangle(379, 110, 389, 110, 384, 101, whiteScript);
    tft.fillTriangle(379, 226, 389, 226, 384, 235, whiteScript);
  } else {
    tft.fillTriangle(379, 110, 389, 110, 384, 101, greyScript);
    tft.fillTriangle(379, 226, 389, 226, 384, 235, greyScript);
  }

  tft.fillRectHGradient(249, 267, 100, 30, pressureColor1, pressureColor2);
  tft.fillRectHGradient(129, 267, 100, 30, temperatureColor1, temperatureColor2);
  tft.setTextDatum(ML_DATUM);
  tft.setTextColor(whiteScript, blackScript);
  smoothText("Lato_Regular_14");
  for (int i = menuStartNetwork; i <= 5; i++) {
    tft.drawString(WiFi.SSID(i), 105, 106 + (spaceText * i), GFXFF);
    if (WiFi.RSSI(i) <= -85) {
      tft.drawSmoothArc(355, 118 + (spaceText * i), 1, 10, 140, 220, wifi_level1, wifi_level1, roundEnd);
    } else if (WiFi.RSSI(i) >= -84 && WiFi.RSSI(i) <= -43) {
      tft.drawSmoothArc(355, 118 + (spaceText * i), 1, 10, 140, 220, wifi_level1, wifi_level2, roundEnd);
      tft.drawSmoothArc(355, 118 + (spaceText * i), 9, 15, 140, 220, wifi_level2, wifi_level2, roundEnd);
    } else if (WiFi.RSSI(i) >= -42 && WiFi.RSSI(i) <= -1){
      tft.drawSmoothArc(355, 118 + (spaceText * i), 1, 10, 140, 220, wifi_level1, wifi_level2, roundEnd);
      tft.drawSmoothArc(355, 118 + (spaceText * i), 9, 15, 140, 220, wifi_level2, wifi_level3, roundEnd);
      tft.drawSmoothArc(355, 118 + (spaceText * i), 14, 19, 140, 220, wifi_level3, blackScript, roundEnd);
    }
  }

  if (language == 1) {
    tft.setTextDatum(MC_DATUM);
    smoothText("Lato_Regular_24");
    tft.setTextColor(whiteScript, blackScript);
    tft.drawString("Select Wi-Fi Network", 240, 74, GFXFF);
    tft.setTextDatum(ML_DATUM);
    tft.drawString("EN-US", 394, 299, GFXFF);
    tft.setTextDatum(MC_DATUM);
    smoothText("Lato_Regular_14");
    tft.setTextColor(whiteScript, temperatureColor1);
    tft.drawString("BACK", 179, 283, GFXFF);
    tft.setTextColor(greyScript, pressureColor1);
    tft.drawString("CONFIRM", 299, 283, GFXFF);
  } else  {
    tft.setTextDatum(MC_DATUM);
    smoothText("Lato_Regular_24");
    tft.setTextColor(whiteScript, blackScript);
    tft.drawString("Seleciona a rede Wi-Fi", 240, 74, GFXFF);
    tft.setTextDatum(ML_DATUM);
    tft.drawString("PT-BR", 394, 299, GFXFF);
    tft.setTextDatum(MC_DATUM);
    smoothText("Lato_Regular_14");
    tft.setTextColor(whiteScript, temperatureColor1);
    tft.drawString("VOLTAR", 179, 283, GFXFF);
    tft.setTextColor(greyScript, pressureColor1);
    tft.drawString("CONFIRMAR", 299, 283, GFXFF);
  }
}

void scrollUp() {
  if (selectNetwork > 0) {
    selectNetwork --;
    if (selectNetwork < menuStartNetwork) {
      menuStartNetwork --;
      menuEndNetwork --;
    }
    menuNetworks();
  }
}

void scrollDown() {
  if (selectNetwork < numNetworks - 1) {
    selectNetwork ++;
    if (selectNetwork > menuEndNetwork) {
      menuStartNetwork ++;
      menuEndNetwork ++;
    }
    menuNetworks();
  }
}

void textBoxName(int keys) {
  Serial.print(keys);
  Serial.print(":  ");
  switch (keys) {
    case 1 : key = ' '; break;
    case 2 : key = ' '; break;
    case 3 : key = ' '; break;
    case 4 : key = ' '; break;
    case 5 : key = ' '; break;
    case 6 : key = ' '; break;
    case 7 : key = ' '; break;
    case 8 : keyBackspace(); break;
    case 9 : key = ' '; break; 
    case 10: enter(); break;
    case 11: key = ' '; break;
    case 12: key = ' '; break;
    case 13: key = ' '; break;
    case 14: key = ' '; break;
    case 15: key = ' '; break;
    case 16: key = ' '; break;
    case 17: key = ' '; break;
    case 18: key = ' '; break;
    case 19: key = ' '; break;
    case 20: key = ' '; break;
    case 21: key = ' '; break;
    case 22: key = ' '; break;
    case 23: key = ' '; break;
    case 24: key = ' '; break;
    case 25: key = ' '; break;
    case 26: key = ' '; break;
    case 27: key = ' '; break;
    case 28: key = ' '; break;
    case 29: key = ' '; break;
    case 30: key = ' '; break;
    case 31: key = ' '; break;
    case 32: key = ' '; break;
    case 33: key = '!'; break;
    case 34: key = '"'; break;
    case 35: key = '#'; break;
    case 36: key = '$'; break;
    case 37: key = '%'; break;
    case 38: key = '&'; break;
    case 39: key = ' '; break;
    case 40: key = '('; break;
    case 41: key = ')'; break;
    case 42: key = '*'; break;
    case 43: key = '+'; break;
    case 44: key = ','; break;
    case 45: key = '-'; break;
    case 46: key = '.'; break;
    case 47: key = '/'; break;
    case 48: key = '0'; break;
    case 49: key = '1'; break;
    case 50: key = '2'; break;
    case 51: key = '3'; break;
    case 52: key = '4'; break;
    case 53: key = '5'; break;
    case 54: key = '6'; break;
    case 55: key = '7'; break;
    case 56: key = '8'; break;
    case 57: key = '9'; break;
    case 58: key = ':'; break;
    case 59: key = ';'; break;
    case 60: key = '<'; break;
    case 61: key = '='; break;
    case 62: key = '>'; break;
    case 63: key = '?'; break;
    case 64: key = '@'; break;
    case 65: key = 'A'; break;
    case 66: key = 'B'; break;
    case 67: key = 'C'; break;
    case 68: key = 'D'; break;
    case 69: key = 'E'; break;
    case 70: key = 'F'; break;
    case 71: key = 'G'; break;
    case 72: key = 'H'; break;
    case 73: key = 'I'; break;
    case 74: key = 'J'; break;
    case 75: key = 'K'; break;
    case 76: key = 'L'; break;
    case 77: key = 'M'; break;
    case 78: key = 'N'; break;
    case 79: key = 'O'; break;
    case 80: key = 'P'; break;
    case 81: key = 'Q'; break;
    case 82: key = 'R'; break;
    case 83: key = 'S'; break;
    case 84: key = 'T'; break;
    case 85: key = 'U'; break;
    case 86: key = 'V'; break;
    case 87: key = 'W'; break;
    case 88: key = 'X'; break;
    case 89: key = 'Y'; break;
    case 90: key = 'Z'; break;
    case 91: key = '['; break;
    case 92: key = '\ '; break;
    case 93: key = ']'; break;
    case 94: key = '^'; break;
    case 95: key = '_'; break;
    case 96: key = '`'; break;
    case 97: key = 'a'; break;
    case 98: key = 'b'; break;
    case 99: key = 'c'; break;
    case 100: key = 'd'; break;
    case 101: key = 'e'; break;
    case 102: key = 'f'; break;
    case 103: key = 'g'; break;
    case 104: key = 'h'; break;
    case 105: key = 'i'; break;
    case 106: key = 'j'; break;
    case 107: key = 'k'; break;
    case 108: key = 'l'; break;
    case 109: key = 'm'; break;
    case 110: key = 'n'; break;
    case 111: key = 'o'; break;
    case 112: key = 'p'; break;
    case 113: key = 'q'; break;
    case 114: key = 'r'; break;
    case 115: key = 's'; break;
    case 116: key = 't'; break;
    case 117: key = 'u'; break;
    case 118: key = 'v'; break;
    case 119: key = 'w'; break;
    case 120: key = 'x'; break;
    case 121: key = 'y'; break;
    case 122: key = 'z'; break;
    case 123: key = '{'; break;
    case 124: key = '|'; break;
    case 125: key = '}'; break;
    case 126: key = '~'; break;
    case 127: key = ' '; break;
  }

  if ((keys >= 1 && keys <= 127) && !(keys == 8 || keys == 10)) {   //APLICAR AS TECLAS FUNCAO
    if (lenghtText < nameLenght) {
      textKnowName[lenghtText++] = key;
      //tft.fillRect(69, 83, 342, 34, blackScript);
      smoothText("Lato_Regular_24");
      tft.setTextDatum(ML_DATUM);
      if (displayTFT == 20) {
        tft.drawString(textKnowName, 69, 100, GFXFF);
        return;
      } else if (displayTFT == 24) {
        tft.drawString(textKnowPassword, 69, 100, GFXFF);
        return;
      }
    }
  }
  else if (lenghtText < nameLenght) {
    //tft.fillRect(69, 83, 342, 34, blackScript);
    smoothText("Lato_Regular_24");
    tft.setTextDatum(ML_DATUM);
    if (displayTFT == 20) {
      tft.drawString(textKnowName, 69, 100, GFXFF);
      return;
    } else if (displayTFT == 24) {
      tft.drawString(textKnowPassword, 69, 165, GFXFF);
      return;
    }
  }
}

void keyBackspace() {
  if (displayTFT == 20) {
    if (lenghtText > 0) {
      textKnowName[--lenghtText] = '\0';
    }
    tft.fillRect(69, 83, 342, 34, blackScript);
  } else if (displayTFT == 24) {
    if (lenghtText > 0) {
      textKnowPassword[--lenghtText] = '\0';
    }
  }
}

void enter() {
  if (displayTFT == 20) {
    Serial.println(textKnowName);
    textKnowName[--lenghtText];
    displayTFT = 19;
    keyboardClose = 0;
    tft.fillScreen(blackScript);
    userName = textKnowName;
    knowname();
  } else if (displayTFT == 24) {
    Serial.println(textKnowPassword);
    textKnowPassword[--lenghtText];
    displayTFT = 22;
    keyboardClose = 0;
    tft.fillScreen(blackScript);
    password = textKnowPassword;
    knowname();
  }
}

void touch_calibrate() {
  displayTFT = 16;
  uint16_t calData[5]; // REMOVER WHITE WHITE WHITE WHITE

  tft.fillScreen(blackScript);

  smoothText("Lato_Regular_14");
  tft.setTextDatum(MC_DATUM);
  tft.setTextColor(whiteScript, blackScript);

  tft.drawString("Toque nas setas indicadas", 240, 124, GFXFF);
  tft.drawString("Touch in the indicated corners", 240, 154, GFXFF);

  tft.calibrateTouch(calData, greenScript, blackScript, 15);

  touchSet = 3;

  tft.fillScreen(blackScript);

  smoothText("Lato_Regular_24");
  tft.setTextDatum(MC_DATUM);
  tft.setTextColor(whiteScript, blackScript);

  tft.drawString("Calibracao Concluida", 240, 104, GFXFF);
  tft.drawString("Calibration Completed!", 240, 144, GFXFF);

  tft.drawRoundRect(70, 250, 100, 30, 5, temperatureColor2);
  
  tft.drawRoundRect(190, 250, 100, 30, 5, icon_9);
  tft.drawRoundRect(310, 250, 100, 30, 5, humidityColor1);

  smoothText("Lato_Regular_14");
  tft.drawString("Recalibrar", 120, 266, GFXFF);
  tft.drawString("Testar", 240, 266, GFXFF);
  tft.drawString("Sair", 360, 266, GFXFF);

  tft.drawString("To recalibrate press button Mode", 240, 184, GFXFF);
  tft.drawString("Para recalibrar pressione o botao Modo", 240, 200, GFXFF);
}

void testCalibration() {
  if (touchScreenMode == 0) {
    tft.fillScreen(blackScript);
    touchScreenMode ++;
    tft.drawRoundRect(70, 250, 100, 30, 5, nixieColor);
    tft.fillRoundRect(190, 250, 100, 30, 5, autumnMenu);
    tft.drawRoundRect(310, 250, 100, 30, 5, winterMenu);

    smoothText("Lato_Regular_14");
    tft.setTextDatum(MC_DATUM);
    tft.setTextColor(whiteScript, blackScript);
    tft.drawString("Recalibrar", 120, 266, GFXFF);
    tft.setTextColor(whiteScript, autumnMenu);
    tft.drawString("Testar", 240, 266, GFXFF);
    tft.setTextColor(whiteScript, blackScript);
    tft.drawString("Sair", 360, 266, GFXFF);
  }
  displayTFT = 17;
  uint16_t x, y;

  tft.setTextColor(whiteScript, blackScript);
  if (tft.getTouch(&x, &y)) {
    tft.fillRect(10, 0, 40, 35, blackScript);
    tft.setCursor(5, 5, 2);
    tft.printf("x: %i     ", x);
    tft.setCursor(5, 20, 2);
    tft.printf("y: %i    ", y);

    tft.fillCircle(x, y, 1, redScript);

    if (switchPressedTest == 0 && touchScreenMode == 1) {
      touchScreenMode == 0;
      testCalibration();
    }
  }
}

void rgbColorGeiger() {
    byte rValue = map (writerGeiger, 33, 433, 255, 228);
    byte gValue = map (writerGeiger, 33, 433, 184, 152);
    byte bValue = map (writerGeiger, 33, 433, 1, 55);

    geigerColor = rgb2rgb.RGB24toRGB16(rValue,gValue,bValue);
}

// -------------------------
void displayMenu() {
  displayMode ++;
  if (displayMode == 1) {
    selectFunctionDisplay();
  } else if (displayMode == 2) {
    displayMode = 0;
  }
}

void selectFunctionDisplay() {
  // telaMenu = 0 Sistema aguardando comando
  // telaMenu = 1 Exibe display Geiger 
  static unsigned long UtlTime = 0;

  if (UtlTime - period >= 5 * 1000) {
    period = UtlTime;
  }  
  if (displayTFT == 0) {
    switch (telaMenu) {
      case 1:
        telaMenu1();
      break;
      case 2:
        telaMenu2();
      break;
      case 3:
        telaMenu3();
      break;
      case 4:
        telaMenu4();
      break;
      case 5:
        telaMenu5();
      break;
      case 6:
        telaMenu6();
      break;
      case 7:
        telaMenu7();
      break;
      case 8:
        telaMenu8();
      break;
      case 9:
        telaMenu9();
      break;
      case 10:
        telaMenu10();
      break;
      case 11:
        telaMenu11();
      break;
      case 12:
        telaMenu12();
      break;
      case 13:
        telaMenu13();
      break;
      case 14:
        telaMenu14();
      break;
      case 15:
        telaMenu15();
      break;
      case 16:
        touch_calibrate();
      break;
      case 17:
        testCalibration();
      break;
      case 18:
        welcome();
      break;
      default:
        defaultSetup();
    }
  }
}

// ------------------------ TELA DE ABERTURA -------------

void startLogo() {
  bool wait = 1;
  tft.fillScreen(blackScript);
  tft.setSwapBytes(true);
  //tft.pushImage(0, 0, 480, 320, abertura); //white white white white white white ATIVAR PARA USAR

  if (language == 1) {
    tft.setTextDatum(ML_DATUM);
    tft.setTextColor(whiteScript, blackScript);
    smoothText("Lato_Bold_48");
    tft.drawString("MAKING THE", 36, 125, GFXFF);
    tft.drawString("OLD NEW", 36, 185, GFXFF);

    smoothText("Lato_Regular_24");
    tft.drawString("EN-US", 394, 299, GFXFF);
  } else {
    tft.setTextDatum(ML_DATUM);
    tft.setTextColor(whiteScript, blackScript);
    smoothText("Lato_Bold_48");
    tft.drawString("FAZENDO O", 36, 125, GFXFF);
    tft.drawString("ANTIGO NOVO", 36, 185, GFXFF);

    smoothText("Lato_Regular_24");
    tft.drawString("PT-BR", 394, 299, GFXFF);
  }
  wifiLevel();
  batteryLevel();
  lockLevel();

  while (wait) {
    bool pressed = tft.getTouch(&x, &y);
    if (pressed) {
      if (touchSet == 0) {
        touch_calibrate();
        wait = 0;
        break;
      }
    }
  }
}

void defaultSetup() {
  if (screenLoad == 0) {
    tft.fillScreen(blackScript);
    
    tft.setSwapBytes(true);
    tft.pushImage(43, 67, 71, 71, icon1);
    tft.pushImage(124, 67, 71, 71, icon2);
    tft.pushImage(205, 67, 71, 71, icon3);
    tft.pushImage(286, 67, 71, 71, icon4);
    tft.pushImage(367, 67, 71, 71, icon5);

    tft.pushImage(43, 147, 71, 71, icon6);
    tft.pushImage(124, 147, 71, 71, icon7);
    tft.pushImage(205, 147, 71, 71, icon8);
    tft.pushImage(286, 147, 71, 71, icon9);
    tft.pushImage(367, 147, 71, 71, icon10);

    tft.pushImage(43, 227, 71, 71, icon11);
    tft.pushImage(124, 227, 71, 71, icon12);
    tft.pushImage(205, 227, 71, 71, icon13);
    tft.pushImage(286, 227, 71, 71, icon14);
    tft.pushImage(367, 227, 71, 71, icon15);

    wifiLevel();
    batteryLevel();
    lockLevel();
    
    screenLoad = 1;
  }
}

void wifiLevel() {
  switch (wifiStyle) {
    case 1:
      wifiStyle1();
    break;
    case 2:
      wifiStyle2();
    break;
    case 3:
      wifiStyle3();
    break;
    default:
      wifiStyle4();
  }
}

void wifiStyle1() {
  tft.fillCircle(333, 36, 2, septemberColor);
  if (wifiRead == 0) {
    tft.drawSmoothArc(333, 36, 5, 7, 134, 226, septemberColor, blackScript, roundEnd);
    tft.drawSmoothArc(333, 36, 10, 12, 134, 226, septemberColor, blackScript, roundEnd);
    tft.drawSmoothArc(333, 36, 15, 17, 134, 226, septemberColor, blackScript, roundEnd);
  } else if (wifiRead == 1) {
    tft.drawSmoothArc(333, 36, 5, 7, 134, 226, septemberColor, blackScript, roundEnd);
    tft.drawSmoothArc(333, 36, 10, 12, 134, 226, septemberColor, blackScript, roundEnd);
  } else {
    tft.drawSmoothArc(333, 36, 5, 7, 134, 226, septemberColor, blackScript, roundEnd);
  }
}
void wifiStyle2() {
  tft.fillRoundRect(322, 15, 30, 30, 5, februeryColor);
  tft.fillCircle(337, 36, 2, whiteScript);
  if (wifiRead == 0) {
    tft.drawSmoothArc(337, 36, 6, 7, 134, 226, whiteScript, februeryColor, roundEnd);
    tft.drawSmoothArc(337, 36, 11, 12, 134, 226, whiteScript, februeryColor, roundEnd);
    tft.drawSmoothArc(337, 36, 16, 17, 134, 226, whiteScript, februeryColor, roundEnd);
  } else if (wifiRead == 1) {
    tft.drawSmoothArc(337, 36, 6, 7, 134, 226, whiteScript, februeryColor, roundEnd);
    tft.drawSmoothArc(337, 36, 11, 12, 134, 226, whiteScript, februeryColor, roundEnd);
  }  else {
    tft.drawSmoothArc(337, 36, 6, 7, 134, 226, whiteScript, februeryColor, roundEnd);
  }
}
void wifiStyle3() {
  if (wifiRead == 0) {
    tft.drawSmoothArc(330, 38, 0, 2, 179, 269, whiteScript, blackScript, squareEnd);
    tft.drawSmoothArc(330, 38, 6, 7, 179, 269, whiteScript, blackScript, squareEnd);
    tft.drawSmoothArc(330, 38, 11, 12, 179, 269, whiteScript, blackScript, squareEnd);
    tft.drawSmoothArc(330, 38, 16, 17, 179, 269, whiteScript, blackScript, squareEnd);
  }  else if (wifiRead == 1) {
    tft.drawSmoothArc(330, 38, 0, 2, 179, 269, whiteScript, blackScript, squareEnd);
    tft.drawSmoothArc(330, 38, 6, 7, 179, 269, whiteScript, blackScript, squareEnd);
    tft.drawSmoothArc(330, 38, 11, 12, 179, 269, whiteScript, blackScript, squareEnd);
  } else {
    tft.drawSmoothArc(330, 38, 0, 2, 179, 269, whiteScript, blackScript, squareEnd);
    tft.drawSmoothArc(330, 38, 6, 7, 179, 269, whiteScript, blackScript, squareEnd);
  }
}
void wifiStyle4() {
  if (wifiRead == 0) {
    tft.drawSmoothArc(337, 36, 0, 4, 134, 226, whiteScript, februeryColor, roundEnd);
    tft.drawSmoothArc(337, 36, 8, 10, 134, 226, whiteScript, februeryColor, roundEnd);
    tft.drawSmoothArc(337, 36, 14, 16, 134, 226, whiteScript, februeryColor, roundEnd);
  }  else if (wifiRead == 1) {
    tft.drawSmoothArc(337, 36, 0, 4, 134, 226, whiteScript, februeryColor, roundEnd);
    tft.drawSmoothArc(337, 36, 8, 10, 134, 226, whiteScript, februeryColor, roundEnd);
  } else {
    tft.drawSmoothArc(337, 36, 0, 4, 134, 226, whiteScript, februeryColor, roundEnd);
  }
}

void batteryLevel() {
  switch (batteryStyleMode) {
      case 1:
        batteryStyle2();
        break;
      case 2:
        batteryStyle3();
        break;
      case 3:
        batteryStyle4();
      break;
      default:
        batteryStyle1();
  }
}

void batteryStyle1() {
  tft.drawRoundRect(362, 18, 47, 21, 3, whiteScript);
  tft.drawRoundRect(363, 19, 45, 20, 2, whiteScript);
  tft.drawSmoothArc(408, 28, 1, 4, 180, 359, whiteScript, whiteScript, squareEnd);

  tft.fillRoundRect(366, 21, 7, 16, 1, green_battery);
  tft.fillRoundRect(374, 21, 7, 16, 1, green_battery);
  tft.fillRoundRect(382, 21, 7, 16, 1, green_battery);
  tft.fillRoundRect(390, 21, 7, 16, 1, green_battery);
  tft.fillRoundRect(398, 21, 7, 16, 1, green_battery);
}
void batteryStyle2() {
  tft.drawRoundRect(362, 18, 47, 21, 3, whiteScript);
  tft.drawRoundRect(363, 19, 45, 20, 2, whiteScript);
  tft.drawSmoothArc(408, 28, 1, 4, 180, 359, whiteScript, whiteScript, squareEnd);

  tft.fillRoundRect(366, 21, 39, 16, 1, green_battery);
}
void batteryStyle3() {
  tft.drawRoundRect(362, 18, 47, 21, 3, whiteScript);
  tft.drawRoundRect(363, 20, 45, 20, 2, whiteScript);
  tft.drawSmoothArc(408, 28, 1, 4, 180, 359, whiteScript, whiteScript, squareEnd);

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
  tft.drawString("25", 190, 225, GFXFF);
  tft.drawString("30", 223, 225, GFXFF);
  tft.drawString("35", 257, 225, GFXFF);
  tft.drawString("40", 290, 225, GFXFF);
  tft.drawString("45", 324, 225, GFXFF);
  tft.drawString("50", 357, 225, GFXFF);
  tft.drawString("55", 390, 225, GFXFF);
} 

void dosimeterDay() {
  tft.drawLine(32, 208, 32, 213, highValueColor);
  tft.drawLine(33, 208, 33, 213, highValueColor);

  tft.drawLine(132, 208, 132, 213, highValueColor);
  tft.drawLine(133, 208, 133, 213, highValueColor);

  tft.drawLine(232, 208, 232, 213, highValueColor);
  tft.drawLine(233, 208, 233, 213, highValueColor);

  tft.drawLine(332, 208, 332, 213, highValueColor);
  tft.drawLine(333, 208, 333, 213, highValueColor);

  tft.drawLine(432, 208, 432, 213, highValueColor);
  tft.drawLine(433, 208, 433, 213, highValueColor);

  tft.drawLine(80, 208, 80, 212, middleTimeGraph);
  tft.drawLine(181, 208, 181, 212, middleTimeGraph);
  tft.drawLine(282, 208, 282, 212, middleTimeGraph);
  tft.drawLine(382, 208, 382, 212, middleTimeGraph);

  tft.drawPixel(443, 78, redScript);
  tft.drawLine(443, 86, 443, 88, redScript);
  tft.drawLine(443, 96, 443, 98, redScript);
  tft.drawLine(443, 106, 443, 108, redScript);
  tft.drawLine(443, 116, 443, 118, redScript);
  tft.drawLine(443, 126, 443, 128, redScript);
  tft.drawLine(443, 136, 443, 138, redScript);
  tft.drawLine(443, 146, 443, 148, redScript);
  tft.drawLine(443, 156, 443, 158, redScript);
  tft.drawLine(443, 166, 443, 168, redScript);
  tft.drawLine(443, 176, 443, 178, redScript);
  tft.drawLine(443, 186, 443, 188, redScript);
  tft.drawPixel(443, 196, redScript);

  tft.setFreeFont(latoRegular10);
  tft.drawString("100", 450, 185, GFXFF);
  tft.drawString("500", 450, 159, GFXFF);
  tft.drawString("1K", 450, 128, GFXFF);
  tft.drawString("2K", 450, 82, GFXFF);

  tft.setTextDatum(ML_DATUM);
  tft.setTextColor(whiteScript);
  tft.setFreeFont(latoRegular24);

  tft.drawString("0", 26, 228, GFXFF);
  tft.drawString("6", 125, 228, GFXFF);
  tft.drawString("12", 220, 228, GFXFF);
  tft.drawString("18", 318, 228, GFXFF);
  tft.drawString("24", 418, 228, GFXFF);

  tft.setFreeFont(latoRegular14);

  tft.drawString("3", 76, 225, GFXFF);
  tft.drawString("9", 178, 225, GFXFF);
  tft.drawString("15", 274, 225, GFXFF);
  tft.drawString("21", 374, 225, GFXFF);
}

void dosimeterWeek() {
  tft.fillRoundRect(32, 104, 41, 94, 5, icon_11);
  tft.fillRoundRect(92, 104, 41, 94, 5, icon_11);
  tft.fillRoundRect(152, 104, 41, 94, 5, icon_11);
  tft.fillRoundRect(212, 104, 41, 94, 5, icon_11);
  tft.fillRoundRect(272, 104, 41, 94, 5, icon_11);
  tft.fillRoundRect(332, 104, 41, 94, 5, icon_11);
  tft.fillRoundRect(392, 104, 41, 94, 5, icon_11);


  tft.setTextDatum(ML_DATUM);
  tft.setTextColor(whiteScript);
  tft.setFreeFont(latoRegular14);

  tft.drawString("Sun", 41, 225, GFXFF);
  tft.drawString("Mon", 99, 225, GFXFF);
  tft.drawString("Tue", 162, 225, GFXFF);
  tft.drawString("Wed", 218, 225, GFXFF);
  tft.drawString("Thu", 281, 225, GFXFF);
  tft.drawString("Fri", 345, 225, GFXFF);
  tft.drawString("Sat", 403, 225, GFXFF);

  tft.drawPixel(443, 78, redScript);
  tft.drawLine(443, 86, 443, 88, redScript);
  tft.drawLine(443, 96, 443, 98, redScript);
  tft.drawLine(443, 106, 443, 108, redScript);
  tft.drawLine(443, 116, 443, 118, redScript);
  tft.drawLine(443, 126, 443, 128, redScript);
  tft.drawLine(443, 136, 443, 138, redScript);
  tft.drawLine(443, 146, 443, 148, redScript);
  tft.drawLine(443, 156, 443, 158, redScript);
  tft.drawLine(443, 166, 443, 168, redScript);
  tft.drawLine(443, 176, 443, 178, redScript);
  tft.drawLine(443, 186, 443, 188, redScript);
  tft.drawPixel(443, 196, redScript);

  tft.setFreeFont(latoRegular10);
  tft.drawString("100", 450, 185, GFXFF);
  tft.drawString("500", 450, 159, GFXFF);
  tft.drawString("1K", 450, 128, GFXFF);
  tft.drawString("2K", 450, 82, GFXFF);
}

void dosimeterMonth() {
  if (month == 1 || month == 3 || month == 5 || month == 7 || month == 8 || month == 10 || month == 12) {
    monthLengh = 31;
  } else {
    monthLengh = 30;
  }
  if (month == 2) {
    if (year%400 == 0) {
      monthLengh = 29;
    } else if((year%4==0) && (year%100!=0)) {
      monthLengh = 29;
    }else {
      monthLengh = 28;
    }
  }

  tft.drawPixel(443, 78, redScript);
  tft.drawLine(443, 86, 443, 88, redScript);
  tft.drawLine(443, 96, 443, 98, redScript);
  tft.drawLine(443, 106, 443, 108, redScript);
  tft.drawLine(443, 116, 443, 118, redScript);
  tft.drawLine(443, 126, 443, 128, redScript);
  tft.drawLine(443, 136, 443, 138, redScript);
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
  tft.drawString("10", 154, 225, GFXFF);
  tft.drawString("20", 295, 225, GFXFF);

  tft.setFreeFont(latoRegular10);
  tft.drawString("100", 445, 185, GFXFF);
  tft.drawString("500", 445, 159, GFXFF);
  tft.drawString("1K", 445, 128, GFXFF);
  tft.drawString("2K", 445, 82, GFXFF);
}
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
