RicardoCSR/MinervaProject/MufoxLogo.h

// Icon width and height
// Width = 165;
// Height = 165;

const uint16_t MufoxLogo[] PROGMEM = {
    0x2988, 0x2988, 0x2988, 0x2988, 0x2988, 0x2988, 0x2988, 0x2988, 0x2988, 0x2988, 0x2988, 0x2988, 0x2988, 0x2988, 0x2988, 0x2988, 0x2988, 0x2988, 0x2988, 0x2988, 0x2988, 0x2988, 0x2988, 0x2988, 0x2988, 0x2988, 0x2988, 0x2988, 0x2988, 0x2988, 0x2988, 0x2988, 0x2988, 0x2988, 0x2988, 0x2988, 0x2988, 0x2988, 0x2988, 0x2988, 0x2988, 0x2988, 0x2988, 0x2988, 0x2988, 0x2988, 0x2988, 0x2988, 0x2988, 0x2988, 0x2988, 0x2988, 0x2988, 0x2988, 0x2988, 0x2988, 0x2988, 0x2988, 0x2988, 0x2988, 0x2988, 0x2988, 0x2988, 0x2988, 0x2988, 0x2988, 0x2988, 0x2988, 0x2988, 0x2988, 0x2988, 0x2988, 0x2988, 0x2988, 0x2988, 0x2988, 0x2988, 0x2988, 0x2988, 0x2988, 0x2988, 0x2988, 0x2988, 0x2988, 0x2988, 0x2988, 0x2988, 0x2988, 0x2988, 0x2988, 0x2988, 0x2988, 0x2988, 0x2988, 0x2988, 0x2988, 0x2988, 0x2988, 0x2988, 0x2988, 0x2988, 0x2988, 0x2988, 0x2988, 0x2988, 0x2988, 0x2988, 0x2988, 0x2988, 0x2988, 0x2988, 0x2988, 0x2988, 0x2988, 0x2988, 0x2988, 0x2988, 0x2988, 0x2988, 0x2988, 0x2988, 0x2988, 0x2988, 0x2988, 0x2988, 0x2988, 0x2988, 0x2988, 0x2988, 0x2988, 0x2988, 0x2988, 0x2988, 0x2988, 0x2988, 0x2988, 0x2988, 0x2988, 0x2988, 0x2988, 0x2988, 0x2988, 0x2988, 0x2988, 0x2988, 0x2988, 0x2988, 0x2988, 0x2988, 0x2988, 0x2988, 0x2988, 0x2988, 0x2988, 0x2988, 0x2988, 0x2988, 0x2988, 0x2988, 0x2988, 0x2988, 0x2988, 0x2988, 0x2988, 0x2988, 
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
};
