RicardoCSR/MinervaProject/Lato_Regular_24.h

const uint8_t Lato_Regular_24Bitmaps[] PROGMEM = {

	// Bitmap Data:
	0x00, // ' '
	0xCC,0xCC,0xCC,0xCC,0xCC,0xC0,0x00,0xCE,0xC0, // '!'
	0x8A,0x28,0xA2,0x8A,0x20, // '"'
	0x0C,0x60,0x62,0x03,0x30,0x11,0x81,0x8C,0x7F,0xFB,0xFF,0xC3,0x10,0x11,0x81,0x8C,0x3F,0xF9,0xFF,0xC3,0x10,0x19,0x80,0x8C,0x0C,0x60,0x63,0x00, // '#'
	0x03,0x00,0x10,0x03,0xE0,0x7F,0xC7,0x26,0x31,0x01,0x88,0x0C,0x40,0x72,0x01,0xF0,0x03,0xF0,0x0F,0xC0,0x66,0x03,0x18,0x18,0xC0,0xCC,0xE4,0xE3,0xFE,0x07,0xE0,0x08,0x00,0x40,0x02,0x00, // '$'
	0x3C,0x03,0x1F,0x81,0x8C,0x20,0xC3,0x0C,0x60,0xC3,0x18,0x30,0xCC,0x0C,0x66,0x01,0xFB,0x00,0x18,0xC0,0x00,0x67,0x80,0x33,0xF0,0x18,0xC6,0x06,0x21,0x83,0x08,0x21,0x82,0x18,0xC0,0xC4,0x70,0x1E,0x00, // '%'
	0x07,0x80,0x0F,0xE0,0x06,0x18,0x06,0x0C,0x03,0x00,0x00,0xC0,0x00,0x60,0x00,0x18,0x00,0x3E,0x0C,0x31,0xC6,0x38,0x73,0x18,0x1F,0x0C,0x07,0x87,0x01,0xC1,0x81,0xE0,0xFF,0x98,0x1F,0x07,0x00, // '&'
	0xAA,0xA0, // '''
	0x10,0xE3,0x18,0x61,0x8C,0x30,0xC3,0x0C,0x30,0xC3,0x0C,0x18,0x61,0x83,0x0C,0x18, // '('
	0x86,0x18,0xC6,0x18,0xC6,0x31,0x8C,0x63,0x18,0xC6,0x63,0x19,0x8C,0x00, // ')'
	0x08,0x04,0x3A,0xC7,0x83,0xC7,0x59,0x24,0x10, // '*'
	0x06,0x00,0x30,0x01,0x80,0x0C,0x00,0x60,0x7F,0xFB,0xFF,0xC0,0xC0,0x06,0x00,0x30,0x01,0x80,0x0C,0x00, // '+'
	0x6E,0x62,0x4C, // ','
	0xFB,0xE0, // '-'
	0x6E,0x60, // '.'
	0x01,0x80,0x40,0x30,0x0C,0x06,0x01,0x80,0x40,0x30,0x0C,0x06,0x01,0x80,0xC0,0x30,0x08,0x06,0x01,0x80,0xC0,0x30,0x00, // '/'
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
	  {   298,  13,  17,  15,    1,  -17 }, // '2'
	  {   326,  13,  17,  15,    1,  -17 }, // '3'
	  {   354,  14,  17,  15,    0,  -17 }, // '4'
	  {   384,  12,  17,  15,    1,  -17 }, // '5'
	  {   410,  13,  17,  15,    1,  -17 }, // '6'
	  {   438,  13,  17,  15,    1,  -17 }, // '7'
	  {   466,  13,  17,  15,    1,  -17 }, // '8'
	  {   494,  12,  17,  15,    1,  -17 }, // '9'
	  {   520,   4,  12,   7,    2,  -12 }, // ':'
	  {   526,   4,  15,   7,    2,  -12 }, // ';'
	  {   534,  10,  10,  15,    2,  -13 }, // '<'
	  {   547,  11,   6,  15,    2,  -11 }, // '='
	  {   556,  10,  10,  15,    3,  -13 }, // '>'
	  {   569,  10,  17,  12,    1,  -17 }, // '?'
	  {   591,  19,  19,  21,    1,  -16 }, // '@'
	  {   637,  17,  17,  17,    0,  -17 }, // 'A'
	  {   674,  13,  17,  17,    2,  -17 }, // 'B'
	  {   702,  16,  17,  17,    1,  -17 }, // 'C'
	  {   736,  16,  17,  19,    2,  -17 }, // 'D'
	  {   770,  12,  17,  15,    2,  -17 }, // 'E'
	  {   796,  12,  17,  15,    2,  -17 }, // 'F'
	  {   822,  16,  17,  19,    1,  -17 }, // 'G'
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
};
const GFXfont Lato_Regular_24 PROGMEM = {
(uint8_t  *)Lato_Regular_24Bitmaps,(GFXglyph *)Lato_Regular_24Glyphs,0x20, 0x7E, 30};
