RicardoCSR/MinervaProject/Lato_Regular_14.h

const uint8_t Lato_Regular_14Bitmaps[] PROGMEM = {

  // Bitmap Data:
  0x00, // ' '
  0x92,0x49,0x20,0x1B,0x00, // '!'
  0xAA,0xAA,0x00, // '"'
  0x12,0x09,0x05,0x0F,0xE2,0x41,0x20,0x91,0xFC,0x28,0x34,0x12,0x00, // '#'
  0x10,0x21,0xE6,0xA9,0x12,0x1C,0x1C,0x1C,0x28,0x95,0x67,0x84,0x08,0x00, // '$'
  0xE1,0x92,0x22,0x48,0x4B,0x0E,0x40,0x17,0x07,0xA0,0xA2,0x24,0x48,0x93,0x0E,0x00, // '%'
  0x38,0x19,0x04,0x01,0x00,0x20,0x14,0x49,0xB2,0x38,0x86,0x33,0xC7,0x98, // '&'
  0xAA, // '''
  0x4B,0x49,0x24,0x92,0x44,0x80, // '('
  0x84,0x42,0x22,0x22,0x22,0x24,0x4C, // ')'
  0x46,0x99,0xA4,0x00, // '*'
  0x10,0x20,0x40,0x8F,0xC2,0x04,0x08, // '+'
  0xAA, // ','
  0xE0, // '-'
  0x98, // '.'
  0x04,0x10,0x20,0x41,0x02,0x08,0x10,0x20,0x81,0x06,0x00, // '/'
  0x3C,0x33,0x10,0x88,0x6C,0x36,0x1B,0x0C,0x86,0x42,0x33,0x0F,0x00, // '0'
  0x10,0x63,0x44,0x81,0x02,0x04,0x08,0x10,0x21,0xF0, // '1'
  0x79,0x9A,0x10,0x20,0x41,0x06,0x18,0x61,0x83,0xF0, // '2'
  0x79,0x9A,0x10,0x20,0xC3,0x03,0x02,0x85,0x99,0xE0, // '3'
  0x04,0x06,0x07,0x02,0x82,0x43,0x21,0x11,0xFE,0x04,0x02,0x01,0x00, // '4'
  0x7C,0x81,0x02,0x0F,0x81,0x81,0x02,0x05,0x19,0xC0, // '5'
  0x18,0x10,0x20,0x60,0x78,0xCC,0x84,0x86,0x84,0xCC,0x78, // '6'
  0xFE,0x04,0x04,0x08,0x08,0x18,0x10,0x30,0x20,0x60,0x40, // '7'
  0x79,0x9A,0x14,0x2C,0xCF,0x33,0x42,0x85,0x89,0xE0, // '8'
  0x79,0x9A,0x14,0x28,0xCF,0x82,0x0C,0x30,0x41,0x80, // '9'
  0xD0,0x00,0x26, // ':'
  0xD8,0x00,0x26,0x50, // ';'
  0x04,0x18,0xC6,0x06,0x03,0x03,0x00, // '<'
  0xFC,0x00,0x07,0xE0, // '='
  0x83,0x06,0x06,0x33,0x08,0x00, // '>'
  0xF2,0x41,0x84,0x31,0x84,0x00,0x01,0x86,0x00, // '?'
  0x1E,0x04,0x31,0x02,0x47,0x29,0xA5,0x24,0xA8,0x95,0x32,0x9B,0x88,0x01,0x82,0x0F,0x80, // '@'
  0x0C,0x03,0x01,0x40,0x58,0x32,0x08,0x82,0x31,0xFC,0x41,0x90,0x6C,0x08, // 'A'
  0xFC,0xC6,0xC2,0xC2,0xC6,0xF8,0xC6,0xC2,0xC2,0xC6,0xFC, // 'B'
  0x3E,0x31,0xB0,0x10,0x08,0x04,0x02,0x01,0x00,0xC0,0x31,0x8F,0x80, // 'C'
  0xFC,0x30,0xCC,0x13,0x06,0xC0,0xB0,0x2C,0x0B,0x06,0xC1,0x30,0xCF,0xC0, // 'D'
  0xFD,0x83,0x06,0x0C,0x1F,0xB0,0x60,0xC1,0x83,0xF0, // 'E'
  0xFD,0x83,0x06,0x0C,0x1F,0xB0,0x60,0xC1,0x83,0x00, // 'F'
  0x3E,0x30,0xB0,0x10,0x08,0x04,0x02,0x1D,0x02,0xC1,0x30,0x87,0x80, // 'G'
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
};
const GFXglyph Lato_Regular_14Glyphs[] PROGMEM = {
// bitmapOffset, width, height, xAdvance, xOffset, yOffset
    {     0,   1,   1,   5,    0,    0 }, // ' '
    {     1,   3,  11,   5,    1,  -11 }, // '!'
    {     6,   4,   5,   6,    1,  -11 }, // '"'
    {     9,   9,  11,   9,    0,  -11 }, // '#'
    {    22,   7,  15,   9,    1,  -13 }, // '$'
    {    36,  11,  11,  12,    1,  -11 }, // '%'
    {    52,  10,  11,  11,    1,  -11 }, // '&'
    {    66,   2,   4,   4,    1,  -11 }, // '''
    {    67,   3,  14,   5,    1,  -12 }, // '('
    {    73,   4,  14,   5,    0,  -12 }, // ')'
    {    80,   5,   5,   7,    1,  -11 }, // '*'
    {    84,   7,   8,   9,    1,   -9 }, // '+'
    {    91,   2,   4,   4,    1,   -2 }, // ','
    {    92,   4,   1,   6,    1,   -5 }, // '-'
    {    93,   3,   2,   4,    1,   -2 }, // '.'
    {    94,   7,  12,   7,    0,  -11 }, // '/'
    {   105,   9,  11,   9,    0,  -11 }, // '0'
    {   118,   7,  11,   9,    1,  -11 }, // '1'
    {   128,   7,  11,   9,    1,  -11 }, // '2'
    {   138,   7,  11,   9,    1,  -11 }, // '3'
    {   148,   9,  11,   9,    0,  -11 }, // '4'
    {   161,   7,  11,   9,    1,  -11 }, // '5'
    {   171,   8,  11,   9,    1,  -11 }, // '6'
    {   182,   8,  11,   9,    1,  -11 }, // '7'
    {   193,   7,  11,   9,    1,  -11 }, // '8'
    {   203,   7,  11,   9,    1,  -11 }, // '9'
    {   213,   3,   8,   5,    1,   -8 }, // ':'
    {   216,   3,  10,   5,    1,   -8 }, // ';'
    {   220,   7,   7,   9,    1,   -9 }, // '<'
    {   227,   7,   4,   9,    1,   -8 }, // '='
    {   231,   6,   7,   9,    2,   -9 }, // '>'
    {   237,   6,  11,   7,    1,  -11 }, // '?'
    {   246,  11,  12,  13,    1,  -10 }, // '@'
    {   263,  10,  11,  10,    0,  -11 }, // 'A'
    {   277,   8,  11,  10,    1,  -11 }, // 'B'
    {   288,   9,  11,  10,    1,  -11 }, // 'C'
    {   301,  10,  11,  12,    1,  -11 }, // 'D'
    {   315,   7,  11,   9,    1,  -11 }, // 'E'
    {   325,   7,  11,   9,    1,  -11 }, // 'F'
    {   335,   9,  11,  11,    1,  -11 }, // 'G'
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
};
const GFXfont Lato_Regular_14 PROGMEM = {
(uint8_t  *)Lato_Regular_14Bitmaps,(GFXglyph *)Lato_Regular_14Glyphs,0x20, 0x7E, 17};
