RicardoCSR/MinervaProject/Lato_Bold_48.h

const uint8_t Lato_Bold_48Bitmaps[] PROGMEM = {

	// Bitmap Data:
	0x00, // ' '
	0x7E,0x7E,0x7E,0x7E,0x7E,0x7E,0x7E,0x7E,0x7E,0x7E,0x7E,0x7E,0x7E,0x7E,0x7E,0x7C,0x7C,0x7C,0x7C,0x7C,0x3C,0x3C,0x00,0x00,0x00,0x00,0x00,0x00,0x3C,0x7E,0xFE,0xFE,0xFE,0x7E,0x3C, // '!'
	0xF8,0xFB,0xE3,0xEF,0x8F,0xBE,0x3E,0xF8,0xFB,0xE3,0xEF,0x8F,0xBE,0x3E,0xF0,0x7B,0xC1,0xEF,0x07,0xBC,0x1E,0x60,0x30, // '"'
	0x00,0x78,0x3C,0x00,0x1F,0x07,0xC0,0x03,0xE0,0xF8,0x00,0x7C,0x1F,0x00,0x0F,0x87,0xC0,0x03,0xE0,0xF8,0x00,0x7C,0x1F,0x00,0x0F,0x83,0xE0,0x01,0xF0,0x7C,0x00,0x3E,0x0F,0x00,0xFF,0xFF,0xFF,0x3F,0xFF,0xFF,0xE7,0xFF,0xFF,0xFC,0xFF,0xFF,0xFF,0x1F,0xFF,0xFF,0x80,0x1F,0x07,0xC0,0x03,0xE1,0xF0,0x00,0xF8,0x3E,0x00,0x1F,0x07,0xC0,0x03,0xE0,0xF8,0x00,0x7C,0x1F,0x01,0xFF,0xFF,0xFE,0x3F,0xFF,0xFF,0xC7,0xFF,0xFF,0xF8,0xFF,0xFF,0xFF,0x0F,0xFF,0xFF,0xE0,0x3E,0x0F,0x80,0x07,0xC1,0xE0,0x00,0xF8,0x7C,0x00,0x3E,0x0F,0x80,0x07,0xC1,0xF0,0x00,0xF8,0x3E,0x00,0x1F,0x07,0xC0,0x03,0xE0,0xF0,0x00,0xF8,0x1E,0x00,0x00, // '#'
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
	  {  1223,  25,  35,  29,    2,  -35 }, // '2'
	  {  1333,  25,  35,  29,    2,  -35 }, // '3'
	  {  1443,  28,  35,  29,    0,  -35 }, // '4'
	  {  1566,  24,  35,  29,    2,  -35 }, // '5'
	  {  1671,  25,  35,  29,    2,  -35 }, // '6'
	  {  1781,  25,  35,  29,    2,  -35 }, // '7'
	  {  1891,  25,  35,  29,    2,  -35 }, // '8'
	  {  2001,  24,  35,  29,    2,  -35 }, // '9'
	  {  2106,   8,  24,  13,    3,  -24 }, // ':'
	  {  2130,   8,  31,  14,    3,  -24 }, // ';'
	  {  2161,  20,  22,  29,    4,  -27 }, // '<'
	  {  2216,  23,  13,  29,    3,  -23 }, // '='
	  {  2254,  20,  22,  29,    5,  -27 }, // '>'
	  {  2309,  19,  35,  23,    2,  -35 }, // '?'
	  {  2393,  38,  39,  41,    2,  -33 }, // '@'
	  {  2579,  35,  35,  34,    0,  -35 }, // 'A'
	  {  2733,  27,  35,  33,    4,  -35 }, // 'B'
	  {  2852,  30,  35,  33,    2,  -35 }, // 'C'
	  {  2984,  32,  35,  38,    4,  -35 }, // 'D'
	  {  3124,  23,  35,  29,    4,  -35 }, // 'E'
	  {  3225,  23,  35,  28,    4,  -35 }, // 'F'
	  {  3326,  31,  35,  36,    2,  -35 }, // 'G'
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
};
const GFXfont Lato_Bold_48 PROGMEM = {
(uint8_t  *)Lato_Bold_48Bitmaps,(GFXglyph *)Lato_Bold_48Glyphs,0x20, 0x7E, 59};
