RicardoCSR/MinervaProject/Lato_Regular_10.h

// Created by http://oleddisplay.squix.ch/ Consider a donation
// In case of problems make sure that you are using the font file with the correct version!
const uint8_t Lato_Regular_10Bitmaps[] PROGMEM = {

	// Bitmap Data:
	0x00, // ' '
	0xAA,0x88, // '!'
	0xDB,0x00, // '"'
	0x28,0x51,0xF2,0x8F,0x8A,0x14,0x00, // '#'
	0x11,0xE5,0x14,0x30,0xA2,0xBE,0x20, // '$'
	0x62,0x4A,0x26,0x0E,0xC1,0x91,0x49,0x18, // '%'
	0x38,0x48,0x20,0x54,0x8C,0x4C,0x76, // '&'
	0x49,0x00, // '''
	0x49,0x49,0x22,0x40, // '('
	0x89,0x24,0x92,0x80, // ')'
	0x6C,0x60, // '*'
	0x42,0x3C,0x84,0x00, // '+'
	0xA0, // ','
	0xC0, // '-'
	0x80, // '.'
	0x10,0x88,0x44,0x23,0x00, // '/'
	0x70,0x92,0x24,0x28,0x89,0x1C,0x00, // '0'
	0x65,0x08,0x42,0x13,0xC0, // '1'
	0x71,0x20,0x82,0x10,0x8F,0x80, // '2'
	0x79,0x20,0x84,0x0A,0x27,0x00, // '3'
	0x10,0x51,0x22,0x4F,0xC1,0x02,0x00, // '4'
	0xF4,0x38,0x21,0x0B,0x80, // '5'
	0x32,0x39,0x29,0x4B,0x80, // '6'
	0xF0,0x88,0x44,0x22,0x00, // '7'
	0x71,0x24,0x8C,0x4B,0x27,0x80, // '8'
	0xE4,0xA5,0xE2,0x33,0x00, // '9'
	0x80,0x80, // ':'
	0x80,0xA0, // ';'
	0x36,0x18,0x20, // '<'
	0xF0,0x3C, // '='
	0xC1,0x99,0x00, // '>'
	0xF0,0x84,0x42,0x01,0x80, // '?'
	0x38,0xC4,0x9A,0xAA,0xCA,0xBC,0xC0,0x3C, // '@'
	0x10,0x28,0x28,0x48,0x7C,0x44,0x82, // 'A'
	0xF2,0x28,0xBC,0x8A,0x2F,0x00, // 'B'
	0x3C,0x81,0x04,0x04,0x08,0x0F,0x00, // 'C'
	0xF9,0x1A,0x14,0x28,0x51,0xBE,0x00, // 'D'
	0xF4,0x21,0xE8,0x43,0xC0, // 'E'
	0xF4,0x21,0xE8,0x42,0x00, // 'F'
	0x3E,0x40,0x40,0x86,0x42,0x42,0x3C, // 'G'
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
};
const GFXglyph Lato_Regular_10Glyphs[] PROGMEM = {
// bitmapOffset, width, height, xAdvance, xOffset, yOffset
	  {     0,   1,   1,   4,    0,    0 }, // ' '
	  {     1,   2,   7,   4,    1,   -7 }, // '!'
	  {     3,   3,   3,   5,    1,   -7 }, // '"'
	  {     5,   7,   7,   7,    0,   -7 }, // '#'
	  {    12,   6,   9,   7,    0,   -8 }, // '$'
	  {    19,   9,   7,   9,    0,   -7 }, // '%'
	  {    27,   8,   7,   8,    0,   -7 }, // '&'
	  {    34,   3,   3,   3,    0,   -7 }, // '''
	  {    36,   3,   9,   4,    0,   -8 }, // '('
	  {    40,   3,   9,   4,    0,   -8 }, // ')'
	  {    44,   4,   3,   5,    1,   -7 }, // '*'
	  {    46,   5,   5,   7,    1,   -6 }, // '+'
	  {    50,   2,   2,   3,    1,   -1 }, // ','
	  {    51,   3,   1,   5,    1,   -3 }, // '-'
	  {    52,   2,   1,   3,    1,   -1 }, // '.'
	  {    53,   5,   7,   6,    0,   -7 }, // '/'
	  {    58,   7,   7,   7,    0,   -7 }, // '0'
	  {    65,   5,   7,   7,    1,   -7 }, // '1'
	  {    70,   6,   7,   7,    0,   -7 }, // '2'
	  {    76,   6,   7,   7,    0,   -7 }, // '3'
	  {    82,   7,   7,   7,    0,   -7 }, // '4'
	  {    89,   5,   7,   7,    1,   -7 }, // '5'
	  {    94,   5,   7,   7,    1,   -7 }, // '6'
	  {    99,   5,   7,   7,    1,   -7 }, // '7'
	  {   104,   6,   7,   7,    0,   -7 }, // '8'
	  {   110,   5,   7,   7,    1,   -7 }, // '9'
	  {   115,   2,   5,   4,    1,   -5 }, // ':'
	  {   117,   2,   6,   4,    1,   -5 }, // ';'
	  {   119,   5,   4,   7,    1,   -5 }, // '<'
	  {   122,   5,   3,   7,    1,   -5 }, // '='
	  {   124,   5,   4,   7,    1,   -5 }, // '>'
	  {   127,   5,   7,   5,    0,   -7 }, // '?'
	  {   132,   8,   8,   9,    1,   -7 }, // '@'
	  {   140,   8,   7,   8,    0,   -7 }, // 'A'
	  {   147,   6,   7,   7,    1,   -7 }, // 'B'
	  {   153,   7,   7,   8,    0,   -7 }, // 'C'
	  {   160,   7,   7,   9,    1,   -7 }, // 'D'
	  {   167,   5,   7,   7,    1,   -7 }, // 'E'
	  {   172,   5,   7,   7,    1,   -7 }, // 'F'
	  {   177,   8,   7,   8,    0,   -7 }, // 'G'
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
};
const GFXfont Lato_Regular_10 PROGMEM = {
(uint8_t  *)Lato_Regular_10Bitmaps,(GFXglyph *)Lato_Regular_10Glyphs,0x20, 0x7E, 13};
