RicardoCSR/MinervaProject/Lato_Regular_12.h

// Created by http://oleddisplay.squix.ch/ Consider a donation
// In case of problems make sure that you are using the font file with the correct version!
const uint8_t Lato_Regular_12Bitmaps[] PROGMEM = {

	// Bitmap Data:
	0x00, // ' '
	0xAA,0x82, // '!'
	0xAA,0xA0, // '"'
	0x34,0x24,0x7E,0x28,0x28,0xFC,0x48,0x50, // '#'
	0x20,0x87,0xA8,0xA1,0x83,0x8A,0xAB,0xC2,0x08, // '$'
	0xE3,0x52,0x29,0x1D,0x01,0x61,0x49,0x25,0x0C, // '%'
	0x70,0x48,0x40,0x60,0xB4,0x9C,0x8C,0xF2, // '&'
	0xA8, // '''
	0x52,0x49,0x24,0x91,0x00, // '('
	0x84,0x42,0x22,0x24,0x44,0x80, // ')'
	0x4E,0xE4, // '*'
	0x20,0x82,0x3E,0x20,0x80, // '+'
	0xA8, // ','
	0xE0, // '-'
	0x80, // '.'
	0x08,0x41,0x04,0x20,0x84,0x10,0xC0, // '/'
	0x38,0x44,0x44,0x86,0x86,0x44,0x44,0x38, // '0'
	0x21,0x8A,0x08,0x20,0x82,0x3E, // '1'
	0x72,0x20,0x82,0x10,0x84,0x3E, // '2'
	0x72,0x20,0x8C,0x08,0x28,0x9C, // '3'
	0x08,0x18,0x28,0x68,0x48,0xFE,0x08,0x08, // '4'
	0x7A,0x0F,0x02,0x08,0x20,0xBC, // '5'
	0x10,0x84,0x3C,0x8A,0x28,0x9C, // '6'
	0xF8,0x21,0x84,0x20,0x84,0x30, // '7'
	0x72,0x28,0x9C,0x8A,0x28,0x9C, // '8'
	0x72,0x28,0xA2,0x78,0x42,0x10, // '9'
	0x80,0x20, // ':'
	0x80,0x2A, // ';'
	0x08,0x46,0x30,0x30,0x20, // '<'
	0xF8,0x0F,0x80, // '='
	0x83,0x03,0x06,0x62,0x00, // '>'
	0xF0,0x20,0x84,0x20,0x00,0x08, // '?'
	0x3C,0x10,0x88,0x12,0x72,0xA4,0xA9,0x2A,0x52,0xF8,0x41,0x0F,0x80, // '@'
	0x18,0x0C,0x0D,0x04,0x82,0x63,0xF1,0x09,0x02, // 'A'
	0xF9,0x0A,0x17,0xC8,0x50,0xA1,0x7C, // 'B'
	0x3E,0xC4,0x80,0x80,0x80,0x80,0xC2,0x3C, // 'C'
	0xFC,0x43,0x20,0x90,0x68,0x34,0x12,0x19,0xF8, // 'D'
	0xFA,0x08,0x3E,0x82,0x08,0x3E, // 'E'
	0xFA,0x08,0x3E,0x82,0x08,0x20, // 'F'
	0x3C,0xC2,0x80,0x80,0x8E,0x82,0xC2,0x3E, // 'G'
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
};
const GFXglyph Lato_Regular_12Glyphs[] PROGMEM = {
// bitmapOffset, width, height, xAdvance, xOffset, yOffset
	  {     0,   1,   1,   4,    0,    0 }, // ' '
	  {     1,   2,   8,   4,    1,   -8 }, // '!'
	  {     3,   4,   3,   5,    1,   -8 }, // '"'
	  {     5,   8,   8,   8,    0,   -8 }, // '#'
	  {    13,   6,  12,   8,    1,  -10 }, // '$'
	  {    22,   9,   8,  11,    1,   -8 }, // '%'
	  {    31,   8,   8,  10,    1,   -8 }, // '&'
	  {    39,   2,   3,   3,    1,   -8 }, // '''
	  {    40,   3,  11,   4,    1,   -9 }, // '('
	  {    45,   4,  11,   4,    0,   -9 }, // ')'
	  {    51,   4,   4,   6,    1,   -9 }, // '*'
	  {    53,   6,   6,   8,    1,   -7 }, // '+'
	  {    58,   2,   3,   4,    1,   -1 }, // ','
	  {    59,   4,   1,   5,    1,   -4 }, // '-'
	  {    60,   2,   1,   4,    1,   -1 }, // '.'
	  {    61,   6,   9,   6,    0,   -9 }, // '/'
	  {    68,   8,   8,   8,    0,   -8 }, // '0'
	  {    76,   6,   8,   8,    1,   -8 }, // '1'
	  {    82,   6,   8,   8,    1,   -8 }, // '2'
	  {    88,   6,   8,   8,    1,   -8 }, // '3'
	  {    94,   8,   8,   8,    0,   -8 }, // '4'
	  {   102,   6,   8,   8,    1,   -8 }, // '5'
	  {   108,   6,   8,   8,    1,   -8 }, // '6'
	  {   114,   6,   8,   8,    1,   -8 }, // '7'
	  {   120,   6,   8,   8,    1,   -8 }, // '8'
	  {   126,   6,   8,   8,    1,   -8 }, // '9'
	  {   132,   2,   6,   4,    1,   -6 }, // ':'
	  {   134,   2,   8,   4,    1,   -6 }, // ';'
	  {   136,   6,   6,   8,    1,   -7 }, // '<'
	  {   141,   6,   3,   8,    1,   -5 }, // '='
	  {   144,   6,   6,   8,    1,   -7 }, // '>'
	  {   149,   6,   8,   6,    0,   -8 }, // '?'
	  {   155,  10,  10,  11,    1,   -8 }, // '@'
	  {   168,   9,   8,   9,    0,   -8 }, // 'A'
	  {   177,   7,   8,   9,    1,   -8 }, // 'B'
	  {   184,   8,   8,   9,    1,   -8 }, // 'C'
	  {   192,   9,   8,  10,    1,   -8 }, // 'D'
	  {   201,   6,   8,   8,    1,   -8 }, // 'E'
	  {   207,   6,   8,   8,    1,   -8 }, // 'F'
	  {   213,   8,   8,  10,    1,   -8 }, // 'G'
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
};
const GFXfont Lato_Regular_12 PROGMEM = {
(uint8_t  *)Lato_Regular_12Bitmaps,(GFXglyph *)Lato_Regular_12Glyphs,0x20, 0x7E, 15};
