RicardoCSR/MinervaProject/backspace.h

// Icon width and height
// Width = 30;
// Height = 24;

const uint16_t backspace[] PROGMEM = {
    0x3188, 0x2988, 0x2988, 0x2988, 0x2988, 0x2988, 0x2988, 0x2988, 0x31e9, 0xb576, 0xc638, 0xc638, 0xc638, 0xc638, 0xc619, 0xc638, 0xc638, 0xc638, 0xc638, 0xc638, 0xc638, 0xc638, 0xc638, 0xc638, 0xc638, 0xc638, 0xc638, 0xc638, 0xc638, 0x8c72, 
    0x2988, 0x2988, 0x2988, 0x2988, 0x2988, 0x2988, 0x2988, 0x2988, 0x8c92, 0xdedb, 0xdedb, 0xdedb, 0xdedb, 0xdedb, 0xdedb, 0xdedb, 0xdedb, 0xdedb, 0xdedb, 0xdedb, 0xdedb, 0xdedb, 0xdedb, 0xdedb, 0xdedb, 0xdedb, 0xdedb, 0xdedb, 0xdedb, 0xdedb, 
    0x2988, 0x2988, 0x2988, 0x2988, 0x2988, 0x2988, 0x2988, 0x8432, 0xdedb, 0xce79, 0x4a8b, 0x422a, 0x422a, 0x422a, 0x422a, 0x422a, 0x422a, 0x422a, 0x422a, 0x422a, 0x422a, 0x422a, 0x422a, 0x422a, 0x422a, 0x422a, 0x422a, 0x422a, 0xdedb, 0xdedb, 
    0x2988, 0x2988, 0x2988, 0x2988, 0x2988, 0x2988, 0x632e, 0xdedb, 0xdedb, 0x632e, 0x422a, 0x8431, 0x422b, 0x2988, 0x2988, 0x2988, 0x2988, 0x2988, 0x2988, 0x2988, 0x2988, 0x2988, 0x2988, 0x2988, 0x422a, 0x8431, 0x422a, 0x2988, 0xdedb, 0xdedb, 
    0x2988, 0x3188, 0x3188, 0x2988, 0x2988, 0x422a, 0xce79, 0xdedb, 0x8431, 0x2988, 0x8431, 0xdedb, 0xc638, 0x422a, 0x2988, 0x2988, 0x2988, 0x2988, 0x2988, 0x2988, 0x3188, 0x2988, 0x2988, 0x422a, 0xc638, 0xdedb, 0x8431, 0x2988, 0xdedb, 0xdedb, 
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
    0x2988, 0x2988, 0x2988, 0x2988, 0x2988, 0x2988, 0x2988, 0x2988, 0x9cd3, 0xdedb, 0xdedb, 0xdedb, 0xdedb, 0xdedb, 0xdedb, 0xdedb, 0xdedb, 0xdedb, 0xdedb, 0xdedb, 0xdedb, 0xdedb, 0xdedb, 0xdedb, 0xdedb, 0xdedb, 0xdedb, 0xdedb, 0xdedb, 0xdedb, 
    0x2988, 0x2988, 0x2988, 0x3188, 0x2988, 0x2988, 0x2988, 0x2988, 0x39e9, 0xad76, 0xc639, 0xc638, 0xc638, 0xc638, 0xc638, 0xc638, 0xc638, 0xc638, 0xc638, 0xc638, 0xc638, 0xc638, 0xc638, 0xc638, 0xc638, 0xc638, 0xc638, 0xc638, 0xc639, 0x8c72
        
};
