RicardoCSR/MinervaProject/backspacePressed.h

// Icon width and height
// Width = 30;
// Height = 24;

const uint16_t backspacePressed[] PROGMEM = {
    0x3188, 0x2988, 0x2988, 0x2988, 0x2988, 0x2988, 0x2988, 0x2988, 0x39e9, 0xad96, 0xc638, 0xc638, 0xc638, 0xc619, 0xc638, 0xc638, 0xc638, 0xc638, 0xc638, 0xc638, 0xc638, 0xc638, 0xc638, 0xc638, 0xc638, 0xc638, 0xc638, 0xc638, 0xc639, 0x8c92, 
    0x2988, 0x2988, 0x2988, 0x2988, 0x2988, 0x2988, 0x3188, 0x3188, 0x8c93, 0xdedb, 0xdedb, 0xdedb, 0xdedb, 0xdedb, 0xdedb, 0xdedb, 0xdedb, 0xdedb, 0xdedb, 0xdedb, 0xdedb, 0xdedb, 0xdedb, 0xdedb, 0xdedb, 0xdedb, 0xdedb, 0xdedb, 0xdedb, 0xdedb, 
    0x2988, 0x2988, 0x3188, 0x2988, 0x2988, 0x2988, 0x2988, 0x8431, 0xdedb, 0xdedb, 0xdedb, 0xdedb, 0xdedb, 0xdedb, 0xdedb, 0xdedb, 0xdedb, 0xdedb, 0xdedb, 0xdedb, 0xdedb, 0xdedb, 0xdedb, 0xdedb, 0xdedb, 0xdedb, 0xdedb, 0xdedb, 0xdedb, 0xdedb, 
    0x2988, 0x2988, 0x2988, 0x2988, 0x2988, 0x2988, 0x632e, 0xdedb, 0xdedb, 0xdedb, 0xdedb, 0xdedb, 0xdedb, 0xdedb, 0xdedb, 0xdedb, 0xdedb, 0xdedb, 0xdedb, 0xdedb, 0xdedb, 0xdedb, 0xdedb, 0xdedb, 0xdedb, 0xdedb, 0xdedb, 0xdedb, 0xdedb, 0xdedb, 
    0x2988, 0x2988, 0x2988, 0x2988, 0x2988, 0x422a, 0xce79, 0xdedb, 0xdedb, 0xdedb, 0xdedb, 0xdedb, 0xdedb, 0xdedb, 0xdedb, 0xdedb, 0xdedb, 0xdedb, 0xdedb, 0xdedb, 0xdedb, 0xdedb, 0xdedb, 0xdedb, 0xdedb, 0xdedb, 0xdedb, 0xdedb, 0xdedb, 0xdedb, 
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
    0x2988, 0x2988, 0x2988, 0x2988, 0x2988, 0x2988, 0x3188, 0x2988, 0x9cd3, 0xdedb, 0xdedb, 0xdedb, 0xdedb, 0xdedb, 0xdedb, 0xdedb, 0xdedb, 0xdedb, 0xdedb, 0xdedb, 0xdedb, 0xdedb, 0xdedb, 0xdedb, 0xdedb, 0xdedb, 0xdedb, 0xdedb, 0xdedb, 0xdedb, 
    0x2988, 0x2988, 0x2988, 0x2988, 0x2988, 0x2988, 0x2988, 0x3188, 0x39e9, 0xad96, 0xc638, 0xc638, 0xc638, 0xc619, 0xc638, 0xc638, 0xc638, 0xc638, 0xc638, 0xc638, 0xc638, 0xc638, 0xc638, 0xc638, 0xc638, 0xc638, 0xc618, 0xc638, 0xc639, 0x8c72
        
};
