RicardoCSR/MinervaProject/shift.h

// Icon width and height
// Width = 24;
// Height = 22;

const uint16_t shift[] PROGMEM = {
    0x2988, 0x3188, 0x3188, 0x2988, 0x2988, 0x2988, 0x2988, 0x2988, 0x2988, 0x2988, 0x422a, 0xad76, 0xc619, 0x422a, 0x3188, 0x2988, 0x2988, 0x2988, 0x2988, 0x2988, 0x2988, 0x3188, 0x3188, 0x2988, 
    0x3188, 0x3188, 0x2988, 0x2988, 0x2988, 0x2988, 0x3188, 0x3188, 0x2988, 0x422a, 0xc638, 0xdedb, 0xdedb, 0xc638, 0x422a, 0x2988, 0x3188, 0x3188, 0x2988, 0x2988, 0x2988, 0x2988, 0x3188, 0x3188, 
    0x2988, 0x2988, 0x2988, 0x2988, 0x2988, 0x2988, 0x2988, 0x2988, 0x422a, 0xc638, 0xdedb, 0xc638, 0xc638, 0xdedb, 0xc638, 0x422a, 0x2988, 0x2988, 0x2988, 0x2988, 0x2988, 0x2988, 0x2988, 0x2988, 
    0x2988, 0x2988, 0x2988, 0x3188, 0x2988, 0x2988, 0x2988, 0x422a, 0xc638, 0xdedb, 0xc638, 0x424a, 0x424a, 0xc638, 0xdedb, 0xc638, 0x422a, 0x2988, 0x2988, 0x2988, 0x3188, 0x2988, 0x2988, 0x2988, 
    0x2988, 0x2988, 0x2988, 0x2988, 0x2988, 0x2988, 0x422a, 0xc638, 0xdedb, 0xc638, 0x422a, 0x2988, 0x2988, 0x422a, 0xc618, 0xdedb, 0xc638, 0x422a, 0x2988, 0x2988, 0x2988, 0x2988, 0x2988, 0x2988, 
    0x2988, 0x2988, 0x2988, 0x2988, 0x2988, 0x422a, 0xc638, 0xdedb, 0xc618, 0x422a, 0x2988, 0x2988, 0x2988, 0x2988, 0x422a, 0xc638, 0xdedb, 0xc638, 0x422a, 0x2988, 0x2988, 0x2988, 0x2988, 0x2988, 
    0x2988, 0x3188, 0x2988, 0x2988, 0x422a, 0xc638, 0xdedb, 0xc638, 0x424a, 0x2988, 0x2988, 0x2988, 0x2988, 0x2988, 0x3188, 0x424a, 0xc638, 0xdedb, 0xc638, 0x422a, 0x2988, 0x2988, 0x3188, 0x2988, 
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
    0x2988, 0x2988, 0x2988, 0x2988, 0x8c92, 0xdedb, 0xdedb, 0xdedb, 0xdedb, 0xdedb, 0xdedb, 0xdedb, 0xdedb, 0xdedb, 0xdedb, 0xdedb, 0xdedb, 0xdedb, 0xdedb, 0x8c72, 0x2988, 0x2988, 0x2988, 0x2988
        
};
