RicardoCSR/MinervaProject/shiftPressed.h

// Icon width and height
// Width = 24;
// Height = 22;

const uint16_t shiftPressed[] PROGMEM = {
    0x2988, 0x2988, 0x2988, 0x2988, 0x2988, 0x2988, 0x2988, 0x2988, 0x3188, 0x2988, 0x422a, 0xad76, 0xc639, 0x422a, 0x2988, 0x3188, 0x2988, 0x2988, 0x2988, 0x2988, 0x2988, 0x2988, 0x2988, 0x2988, 
    0x2988, 0x2988, 0x2988, 0x2988, 0x2988, 0x3188, 0x2988, 0x3188, 0x2988, 0x422a, 0xc638, 0xdedb, 0xdedb, 0xc638, 0x422a, 0x2988, 0x3188, 0x2988, 0x3188, 0x2988, 0x2988, 0x2988, 0x2988, 0x2988, 
    0x2988, 0x2988, 0x2988, 0x2988, 0x2988, 0x2988, 0x3188, 0x2988, 0x422a, 0xc638, 0xdedb, 0xdedb, 0xdedb, 0xdedb, 0xc638, 0x422a, 0x2988, 0x3188, 0x2988, 0x2988, 0x2988, 0x2988, 0x2988, 0x2988, 
    0x2988, 0x2988, 0x2988, 0x2988, 0x2988, 0x2988, 0x2988, 0x422a, 0xc638, 0xdedb, 0xdeda, 0xdedb, 0xdedb, 0xdeda, 0xdedb, 0xc638, 0x422a, 0x2988, 0x2988, 0x2988, 0x2988, 0x2988, 0x2988, 0x2988, 
    0x2988, 0x2988, 0x2988, 0x2988, 0x2988, 0x2988, 0x422a, 0xc619, 0xdedb, 0xdedb, 0xdedb, 0xdedb, 0xdedb, 0xdedb, 0xdedb, 0xdedb, 0xc619, 0x422a, 0x2988, 0x2988, 0x2988, 0x2988, 0x2988, 0x2988, 
    0x2988, 0x3188, 0x2988, 0x2988, 0x2988, 0x422a, 0xc638, 0xdedb, 0xdedb, 0xdedb, 0xdedb, 0xdedb, 0xdedb, 0xdedb, 0xdedb, 0xdedb, 0xdedb, 0xc638, 0x422a, 0x2988, 0x2988, 0x2988, 0x3188, 0x2988, 
    0x2988, 0x2988, 0x3188, 0x2988, 0x422a, 0xc638, 0xdedb, 0xdedb, 0xdedb, 0xdedb, 0xdedb, 0xdedb, 0xdedb, 0xdedb, 0xdedb, 0xdedb, 0xdedb, 0xdedb, 0xc638, 0x422a, 0x2988, 0x3188, 0x2988, 0x2988, 
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
    0x3188, 0x2988, 0x2988, 0x2988, 0x9492, 0xdedb, 0xdedb, 0xdedb, 0xdedb, 0xdedb, 0xdedb, 0xdedb, 0xdedb, 0xdedb, 0xdedb, 0xdedb, 0xdedb, 0xdedb, 0xdedb, 0x8c72, 0x2988, 0x2988, 0x2988, 0x2988
        
};
